phuongmt08/uwb-rtls/docs/assets/diagrams/thesis/chapter4/figure-4-2-firmware-startup-flow.png

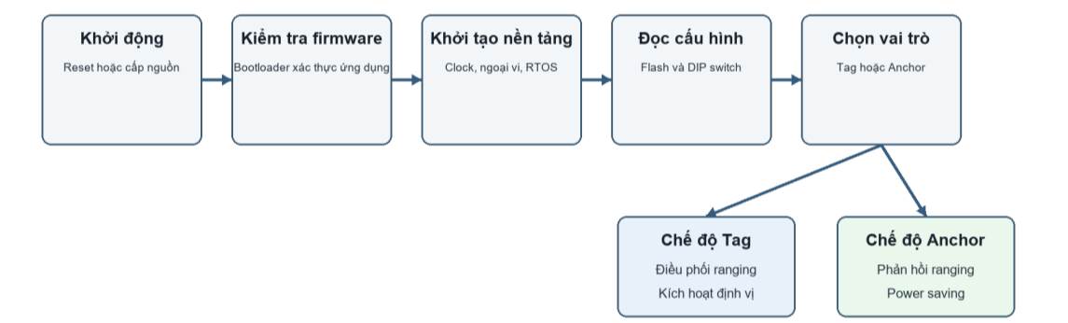
docs/assets/diagrams/thesis/chapter4/figure-4-2-firmware-startup-flow.png
