phuongmt08/uwb-rtls/docs/assets/diagrams/thesis/chapter4/figure-4-7-flash-write-and-swap-flow.png

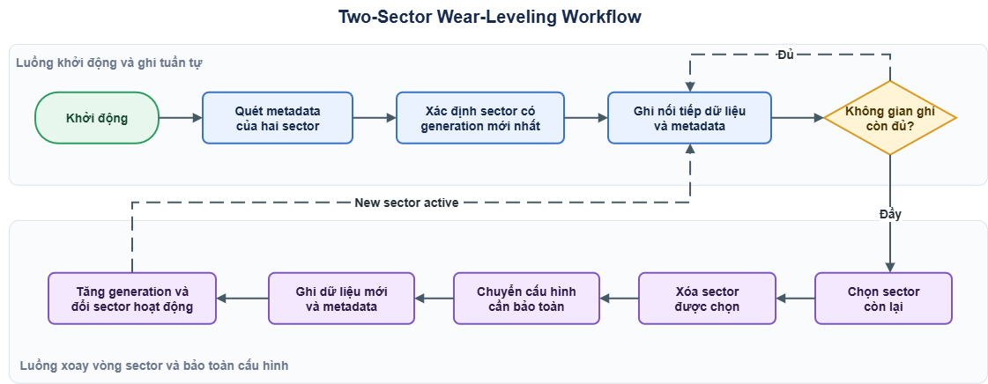
docs/assets/diagrams/thesis/chapter4/figure-4-7-flash-write-and-swap-flow.png
