phuongmt08/uwb-rtls/docs/assets/diagrams/thesis/chapter4/figure-4-18-ble-connection-flow.png

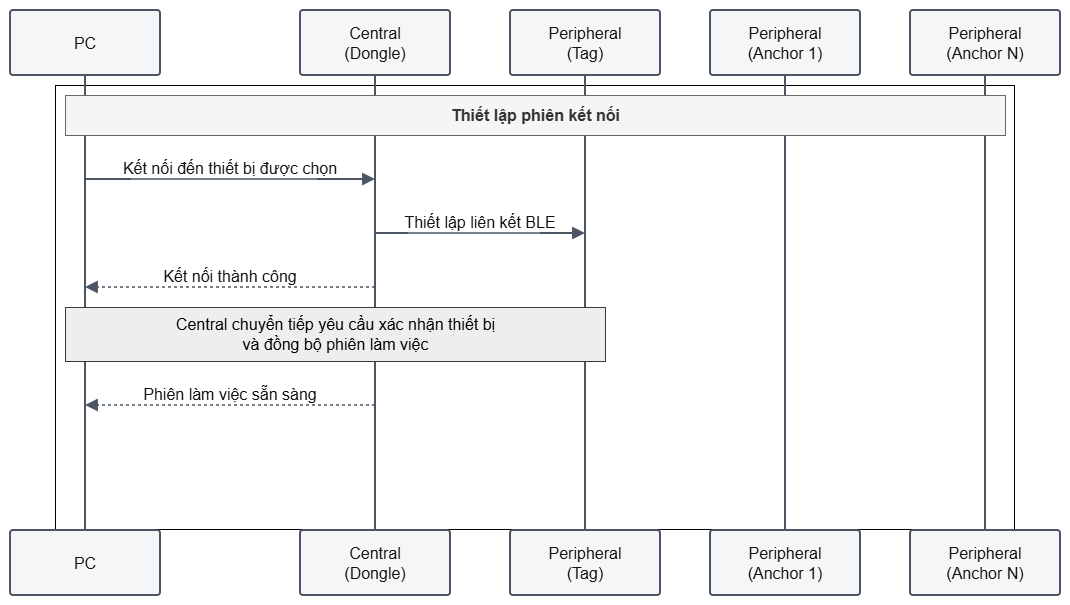
docs/assets/diagrams/thesis/chapter4/figure-4-18-ble-connection-flow.png
