phuongmt08/uwb-rtls/docs/assets/diagrams/thesis/chapter4/figure-4-19-ble-data-exchange-flow.png

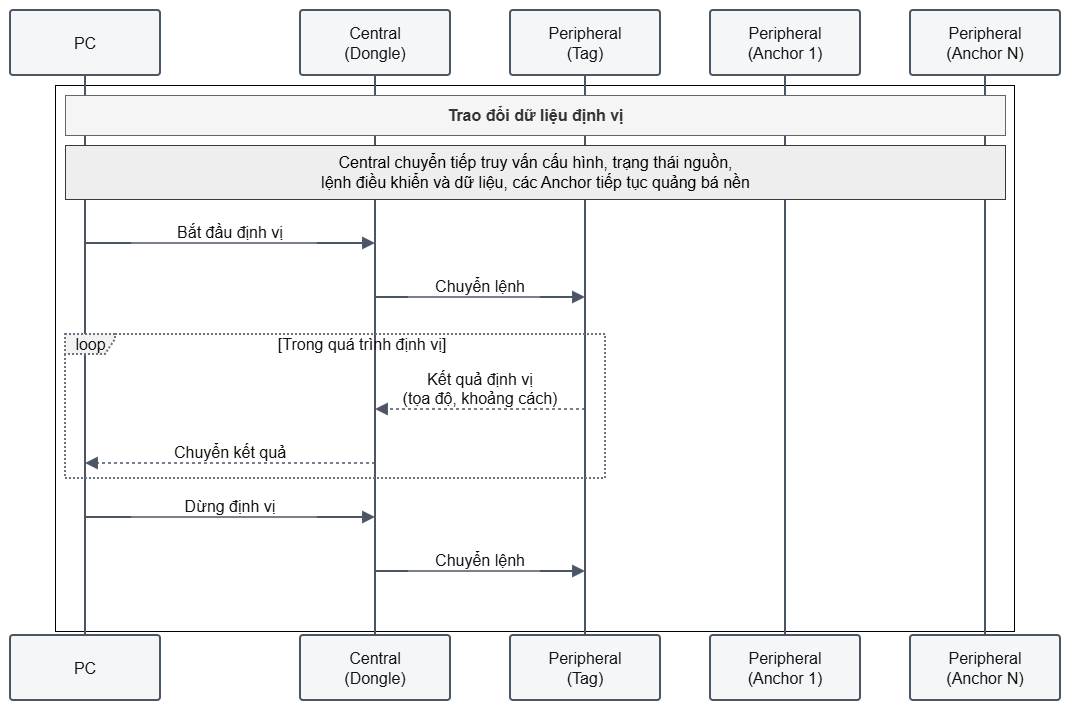
docs/assets/diagrams/thesis/chapter4/figure-4-19-ble-data-exchange-flow.png
