phuongmt08/uwb-rtls/docs/assets/images/thesis/chapter4/figure-4-15-nlos-cir-sample-mask.png

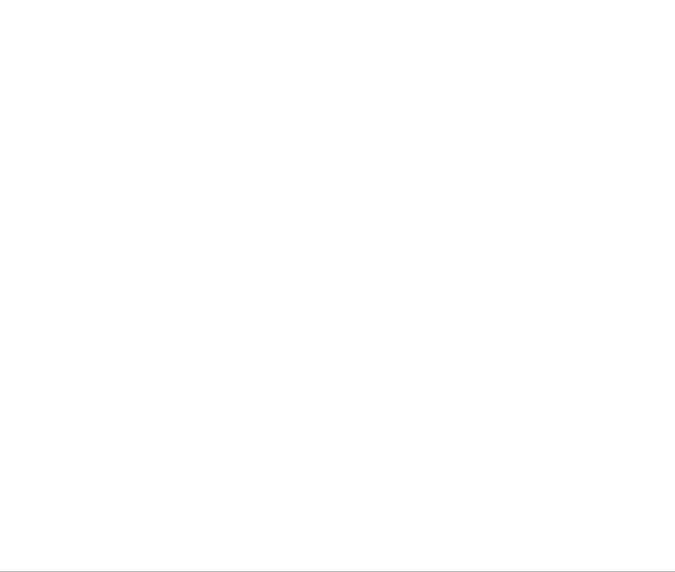
docs/assets/images/thesis/chapter4/figure-4-15-nlos-cir-sample-mask.png
