phuongmt08/uwb-rtls/docs/assets/images/thesis/raw/thesis-image-001.png

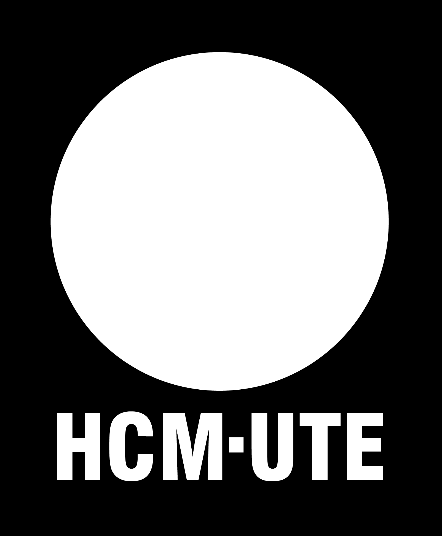
docs/assets/images/thesis/raw/thesis-image-001.png
