phuongmt08/uwb-rtls/docs/assets/images/thesis/raw/thesis-image-028.png

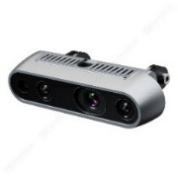
docs/assets/images/thesis/raw/thesis-image-028.png
