phuongmt08/uwb-rtls/docs/assets/images/thesis/raw/thesis-image-029.png

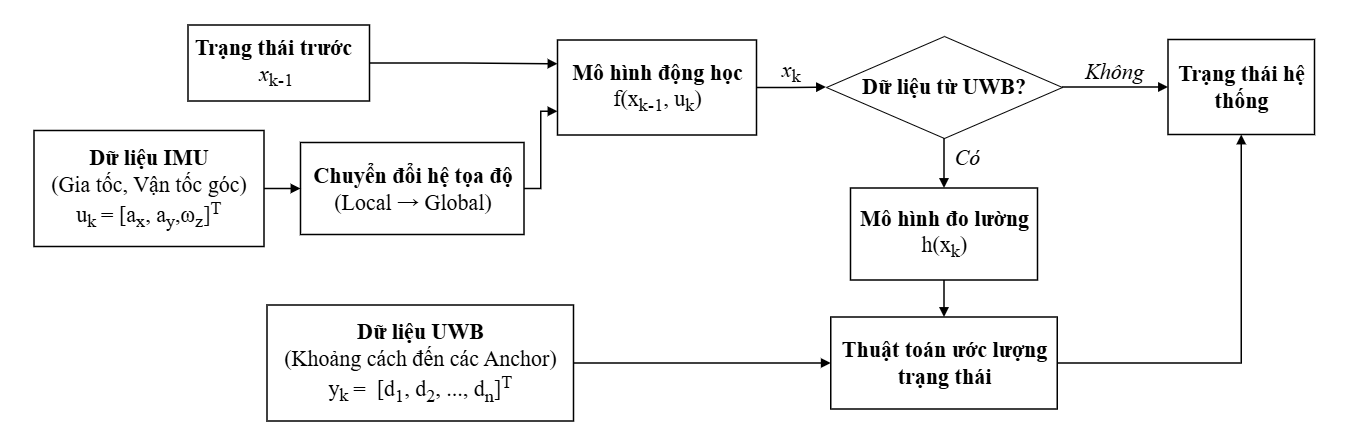
docs/assets/images/thesis/raw/thesis-image-029.png
