phuongmt08/uwb-rtls/docs/assets/images/thesis/raw/thesis-image-034.png

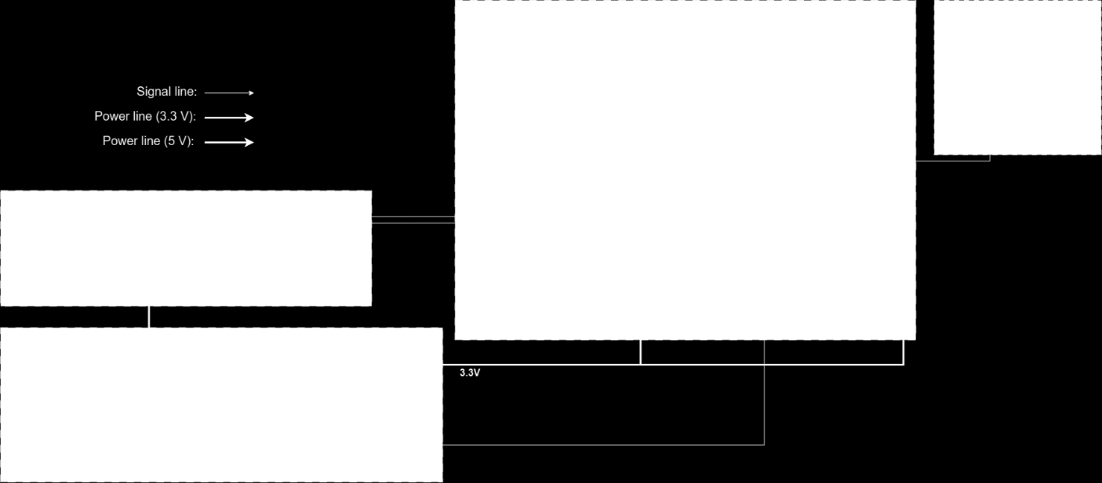
docs/assets/images/thesis/raw/thesis-image-034.png
