phuongmt08/uwb-rtls/docs/assets/images/thesis/raw/thesis-image-037.png

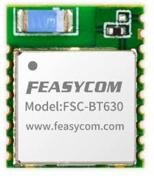
docs/assets/images/thesis/raw/thesis-image-037.png
