phuongmt08/uwb-rtls/docs/assets/images/thesis/raw/thesis-image-058.png

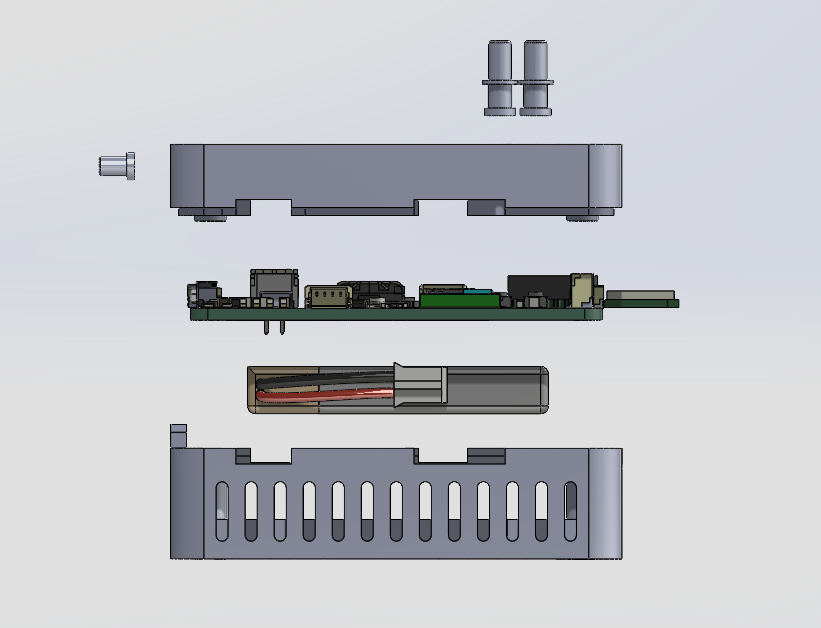
docs/assets/images/thesis/raw/thesis-image-058.png
