phuongmt08/uwb-rtls/docs/assets/images/thesis/raw/thesis-image-059.png

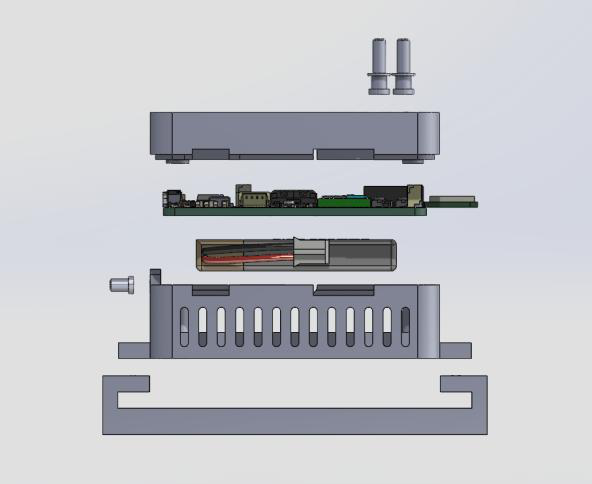
docs/assets/images/thesis/raw/thesis-image-059.png
