phuongmt08/uwb-rtls/docs/assets/images/thesis/raw/thesis-image-092.png

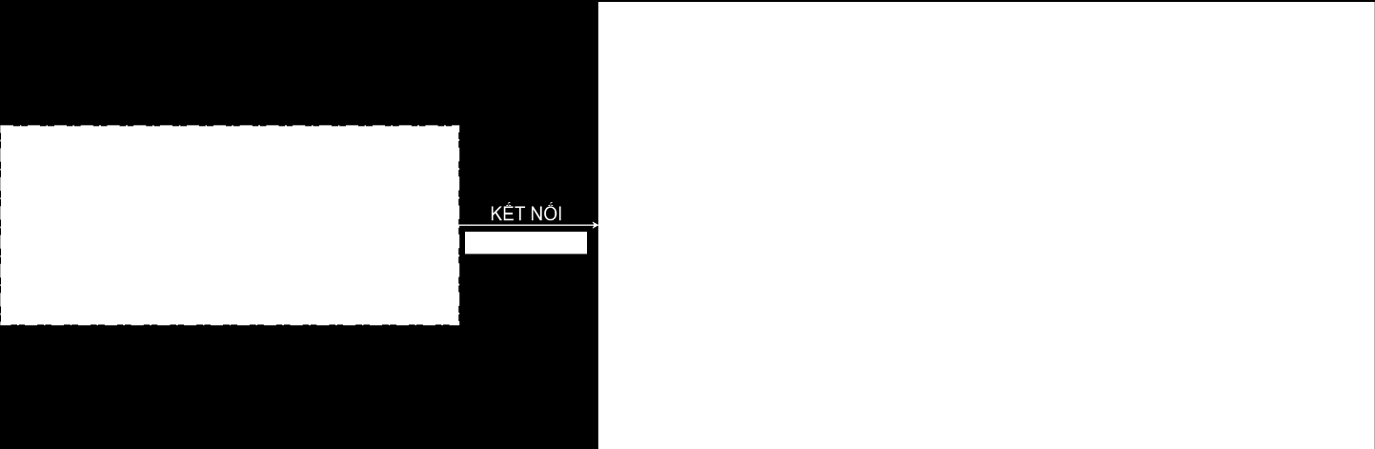
docs/assets/images/thesis/raw/thesis-image-092.png
