phuongmt08/uwb-rtls/docs/assets/images/thesis/raw/thesis-image-096.png

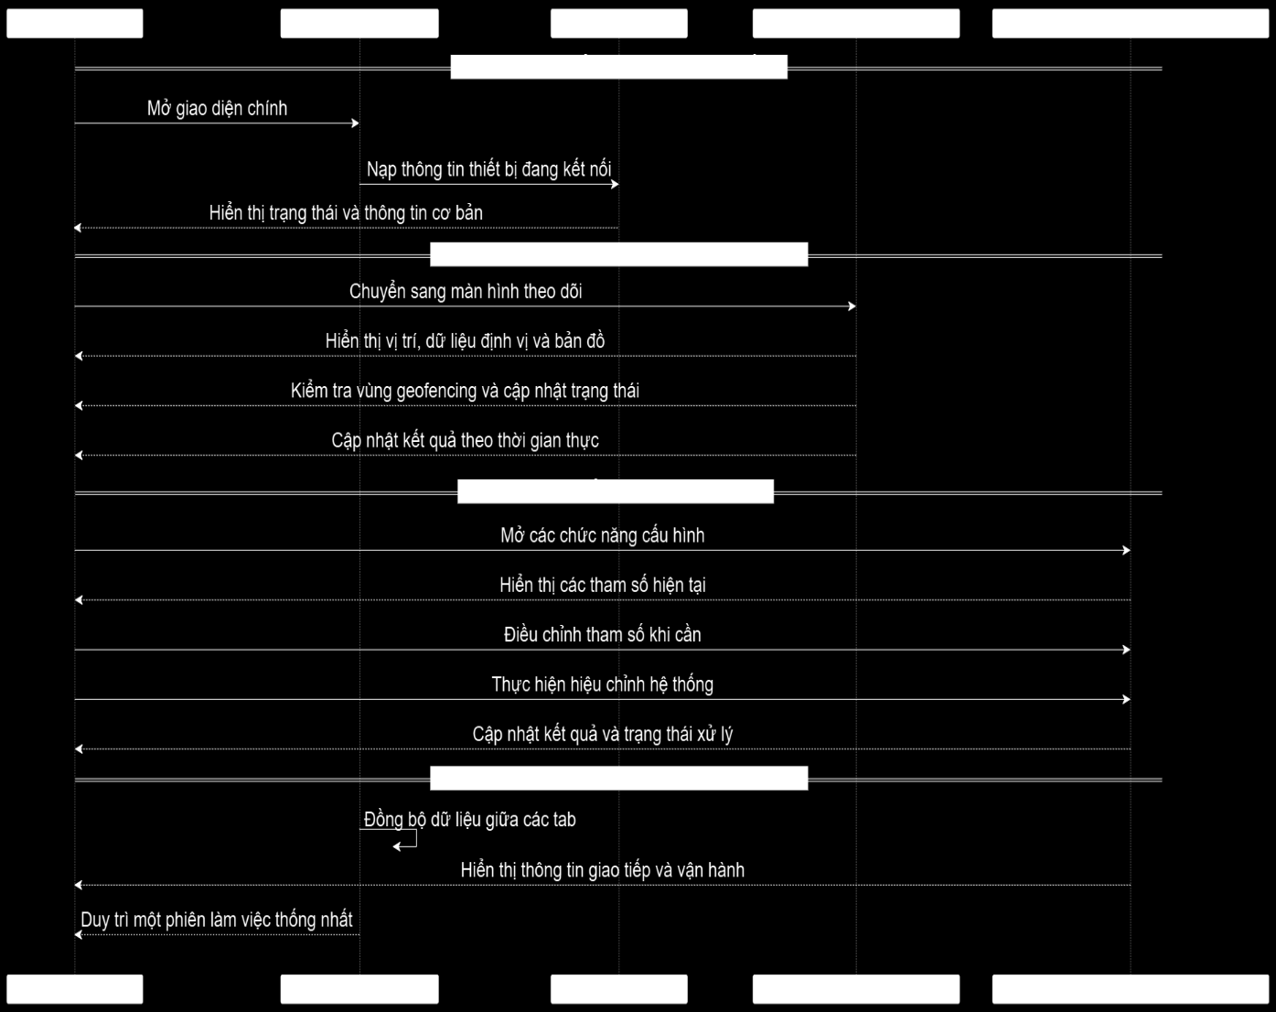
docs/assets/images/thesis/raw/thesis-image-096.png
