phuongmt08/uwb-rtls/docs/assets/images/thesis/raw/thesis-image-098.png

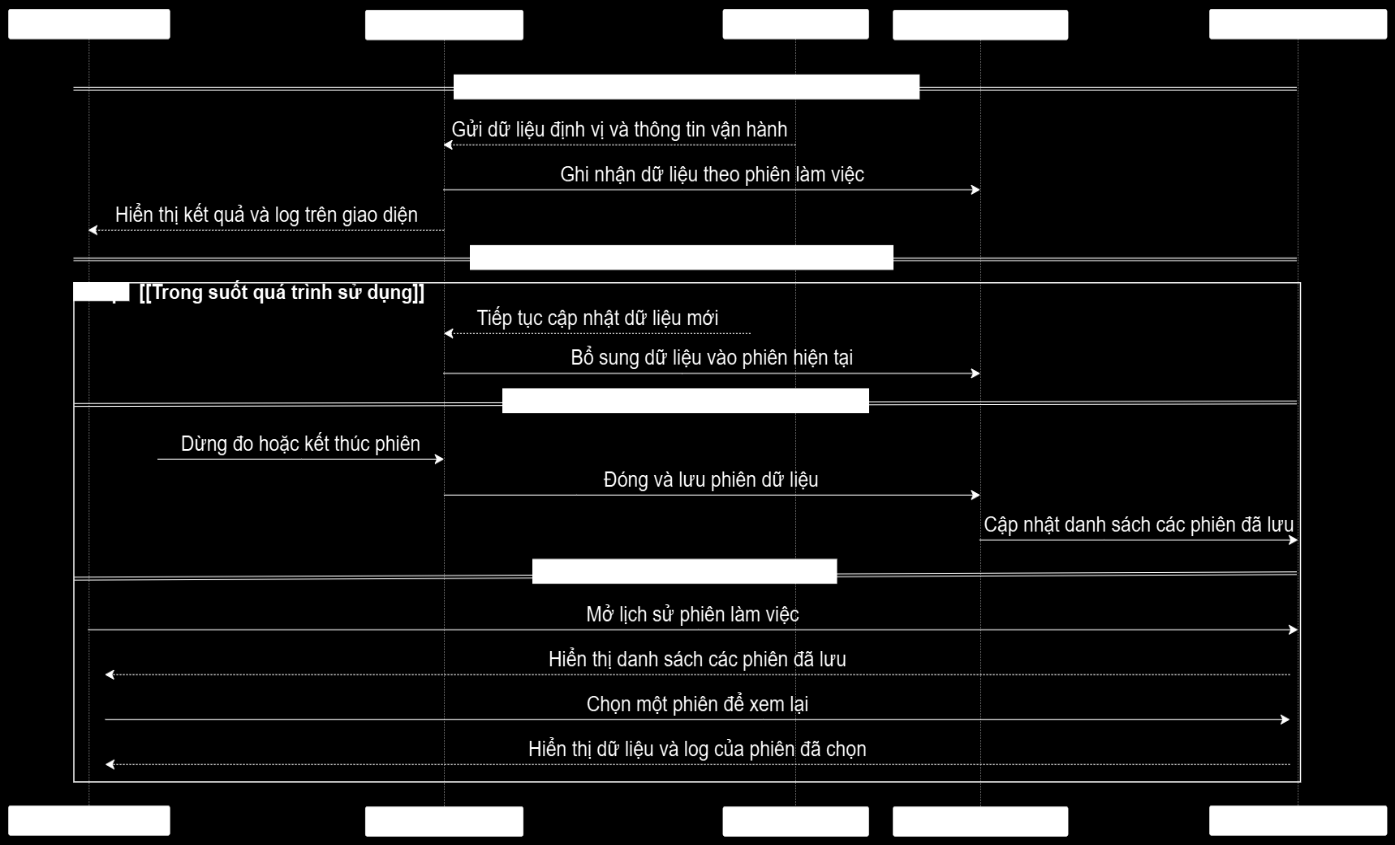
docs/assets/images/thesis/raw/thesis-image-098.png
