phuongmt08/uwb-rtls/docs/assets/images/thesis/raw/thesis-image-110.png

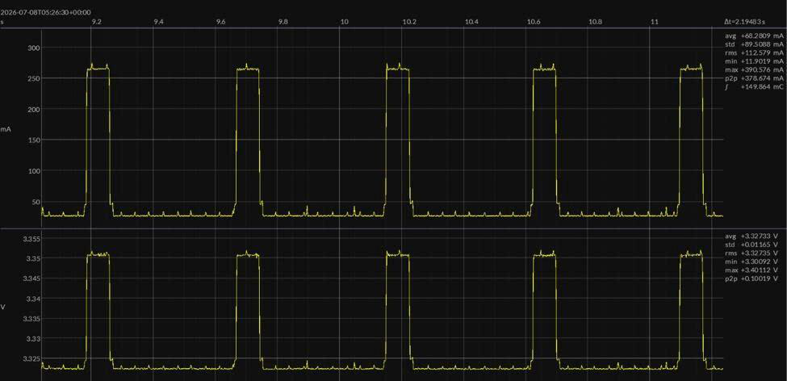
docs/assets/images/thesis/raw/thesis-image-110.png
