phuongmt08/uwb-rtls/docs/assets/images/thesis/raw/thesis-image-129.png

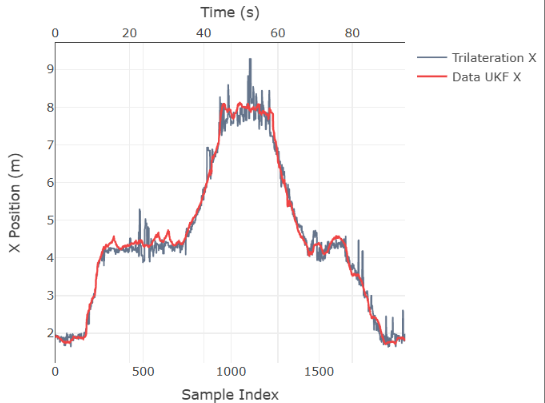
docs/assets/images/thesis/raw/thesis-image-129.png
