phuongmt08/uwb-rtls/docs/assets/images/thesis/raw/thesis-image-131.png

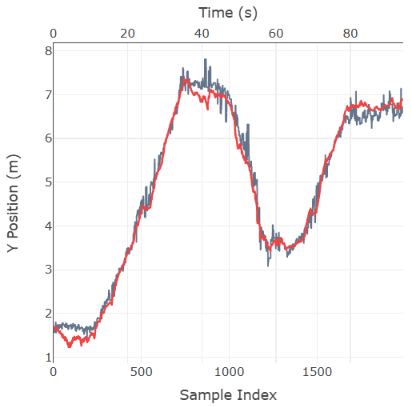
docs/assets/images/thesis/raw/thesis-image-131.png
