phuongmt08/uwb-rtls/docs/assets/images/thesis/raw/thesis-image-139.png

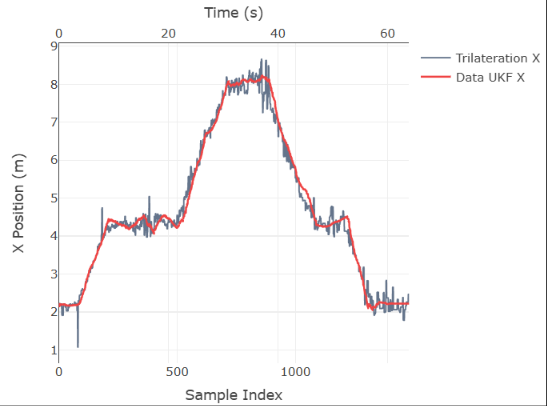
docs/assets/images/thesis/raw/thesis-image-139.png
