phuongmt08/uwb-rtls/docs/assets/images/thesis/raw/thesis-image-141.png

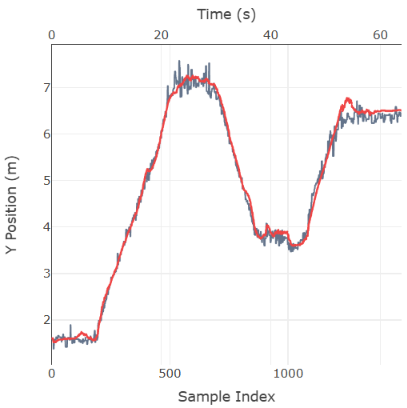
docs/assets/images/thesis/raw/thesis-image-141.png
