phuongmt08/uwb-rtls/hardware/anchor/rev0.1/rev0.1_backward.png

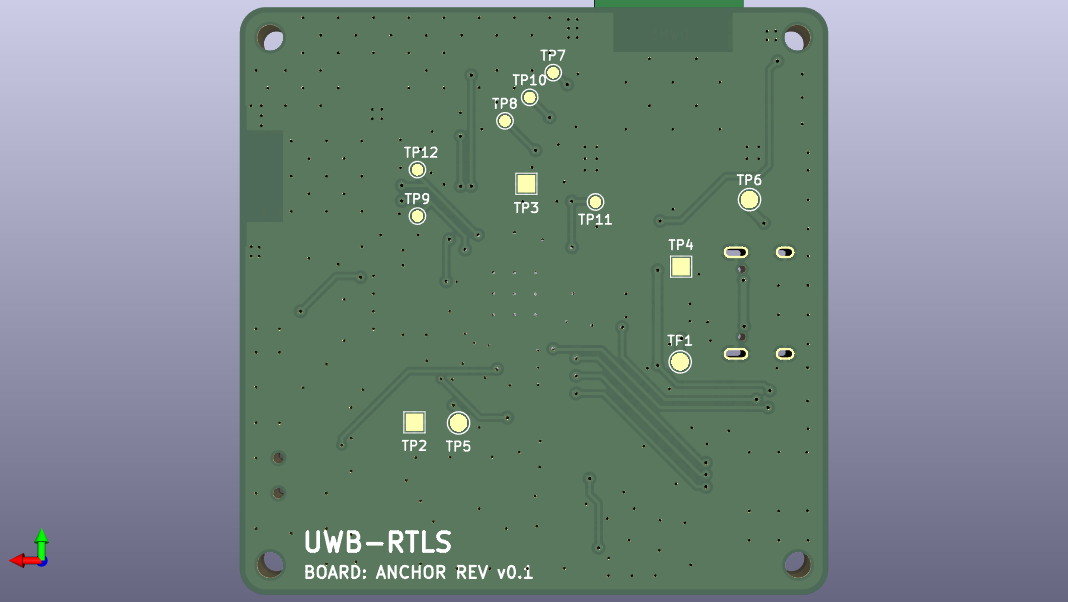
hardware/anchor/rev0.1/rev0.1_backward.png
