phuongmt08/uwb-rtls/hardware/anchor/rev0.1/rev0.1_forward.png

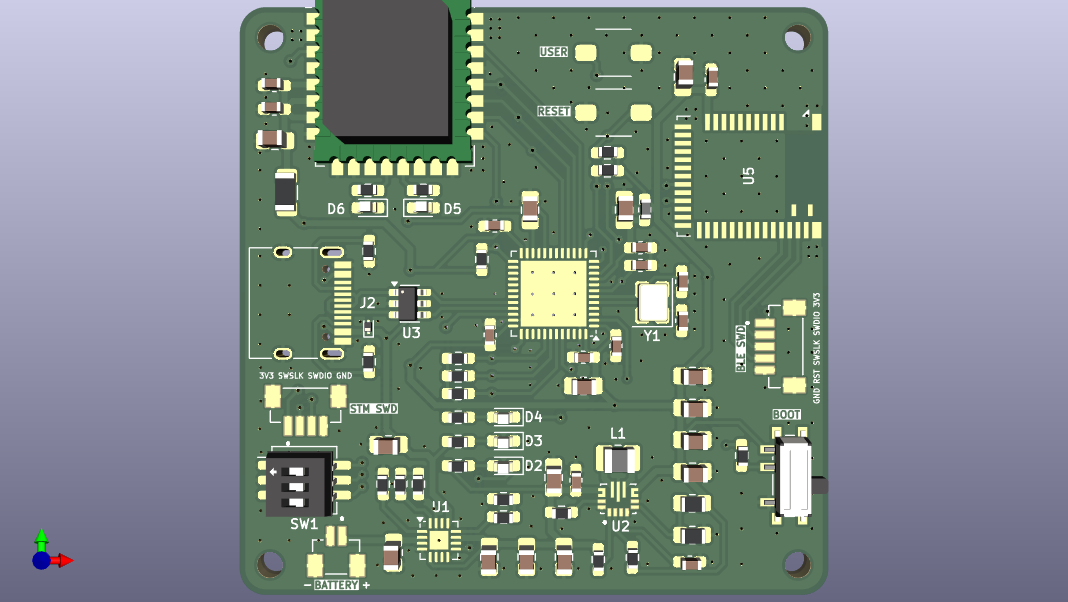
hardware/anchor/rev0.1/rev0.1_forward.png
