phuongmt08/uwb-rtls/tmp/pdfs/you2020/page-03.png

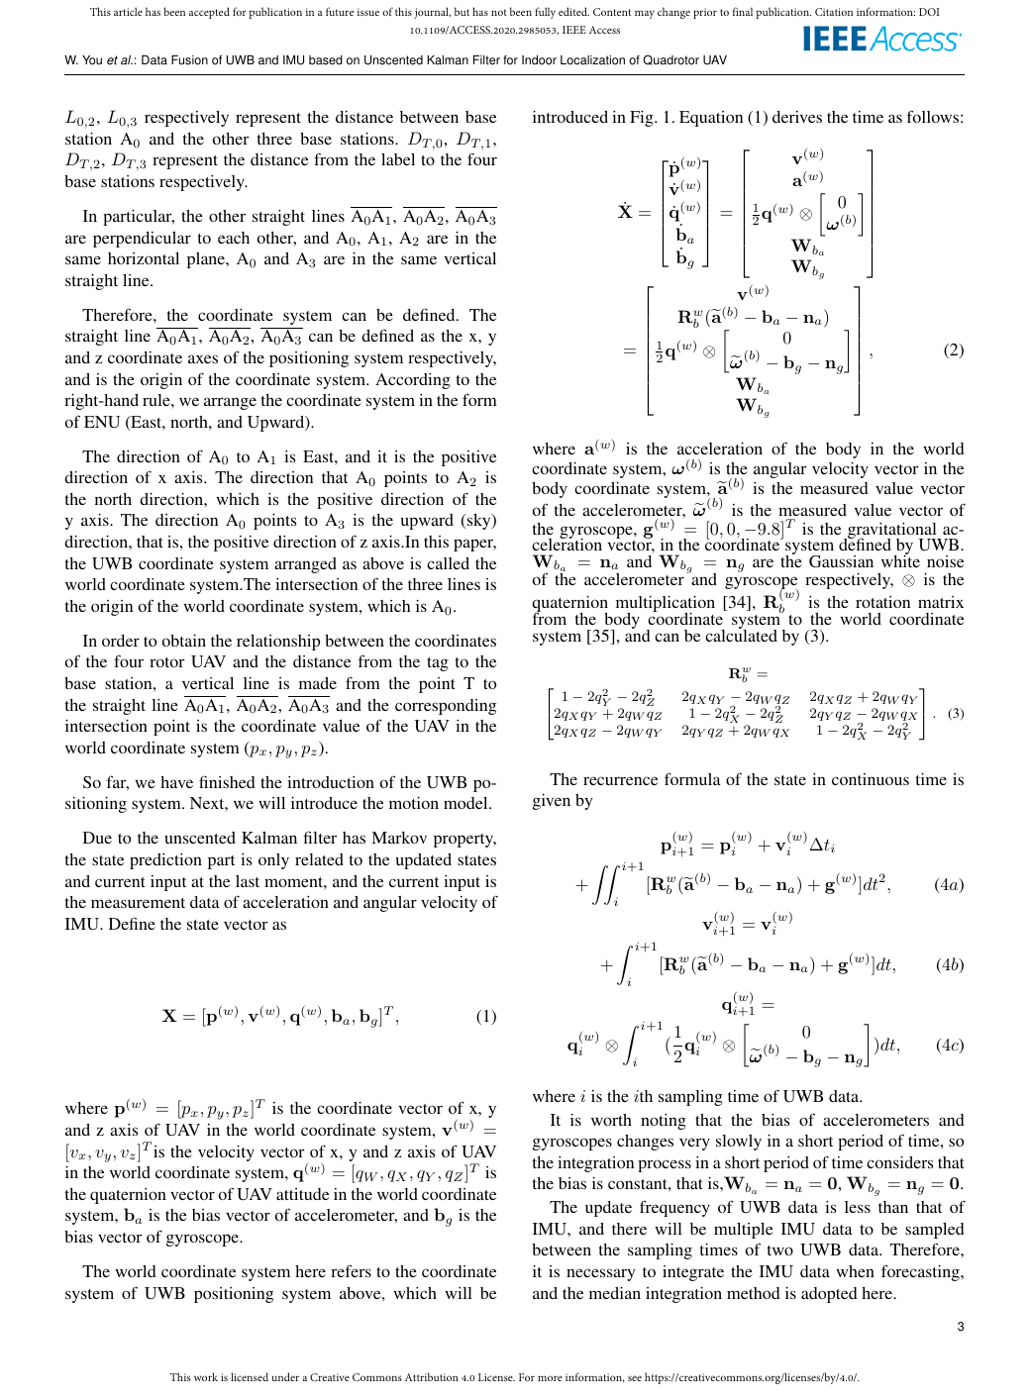
tmp/pdfs/you2020/page-03.png
