phuongmt08/uwb-rtls/tmp/pdfs/you2020/page-05.png

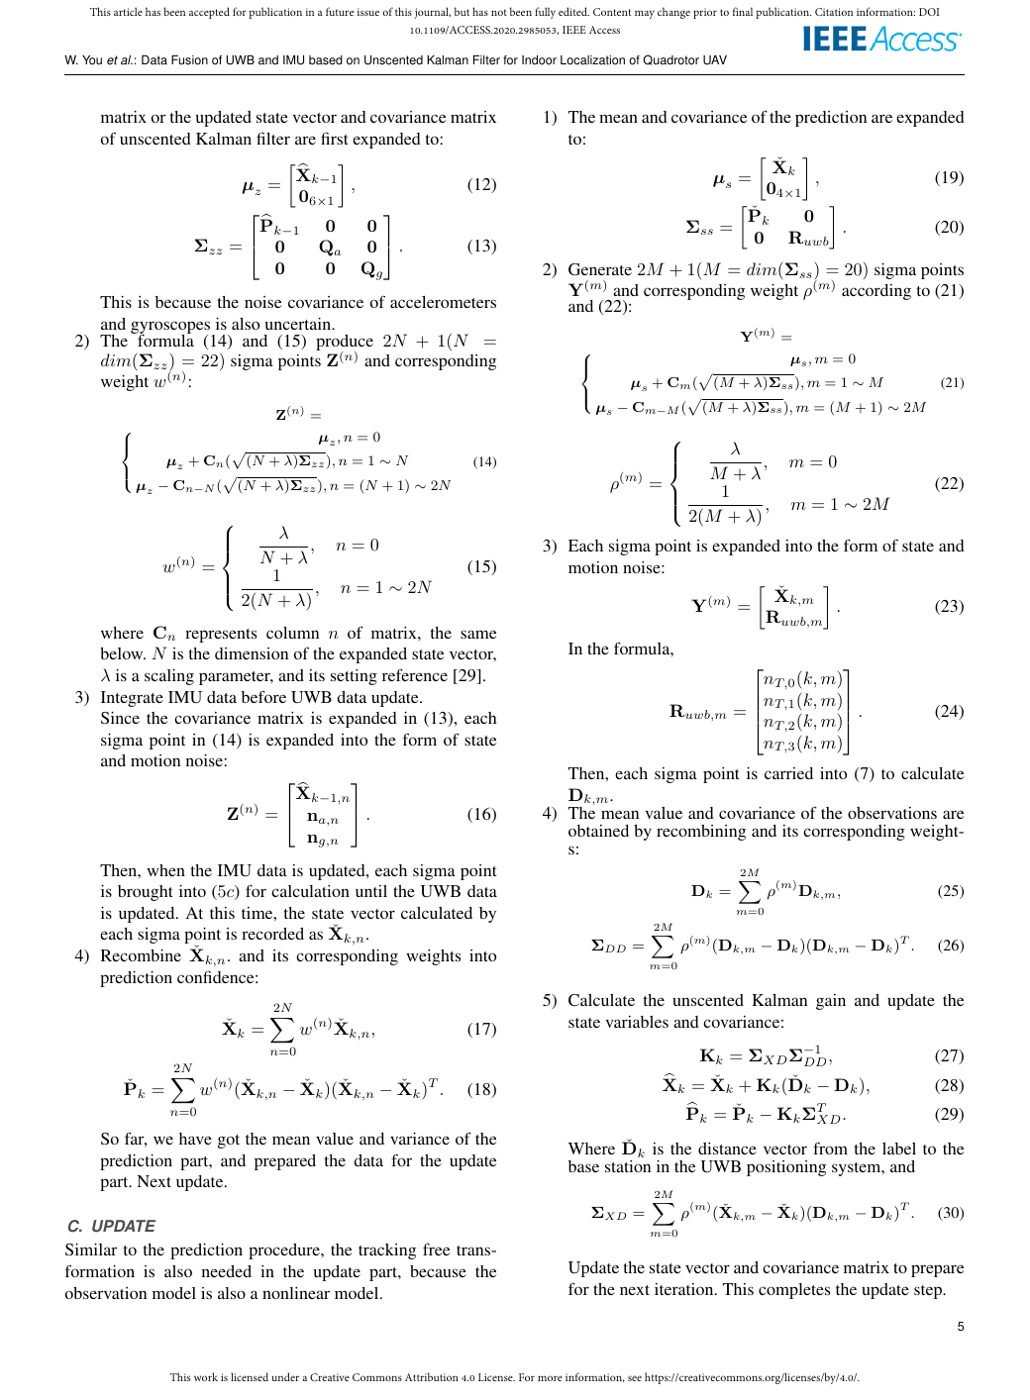
tmp/pdfs/you2020/page-05.png
