phuongmt08/uwb-rtls/firmware/uwb/sys/sys_sensor_fusion.c

/**
 * @file       sys_sensor_fusion.c
 * @copyright  [Your Copyright]
 * @license    [Your License]
 * @version    1.0.0
 * @date       25/03/26
 * @author     Dong Son
 *
 * @brief
 */
/* Includes ----------------------------------------------------------- */
#include "config.h"
#include "sys_sensor_fusion.h"
#include "bsp_imu.h"
#include "positioning_config.h"
#include "bsp_io.h"
#include "bsp_util.h"
#include "err.h"
#include "mw_filter.h"
#include "network/network_cmd.h"
#include <stddef.h>
#include <math.h>
#include <string.h>
#include <stdio.h>
#include "sys_config.h"
#include "ble/sys_ble_peripheral.h"
#include "sys_logger.h"
#include "cmsis_os2.h"
#include "app_rtos_handles.h"

/* Private defines ---------------------------------------------------- */
#define NUM_STATE     			8
#define NUM_PREDICT_NOISE     	3
#define NUM_UPDATE_NOISE     	3
#define N       				(NUM_STATE + NUM_PREDICT_NOISE)
#define M						(NUM_STATE + NUM_UPDATE_NOISE)
#define NUM_PREDICT_SIGMA  		(2*N + 1)
#define NUM_UPDATE_SIGMA  		(2*M + 1)

#define UKF_ALPHA               SYS_FUSION_UKF_ALPHA
#define UKF_KAPPA               SYS_FUSION_UKF_KAPPA
#define UKF_BETA                SYS_FUSION_UKF_BETA
#define N_PLUS_LAMBDA_N         (UKF_ALPHA * UKF_ALPHA * (N + UKF_KAPPA))
#define UKF_LAMBDA_N  			(N_PLUS_LAMBDA_N - N)
#define GAMMA_N       			sqrtf(N_PLUS_LAMBDA_N)
#define M_PLUS_LAMBDA_M         (UKF_ALPHA * UKF_ALPHA * (M + UKF_KAPPA))
#define UKF_LAMBDA_M  			(M_PLUS_LAMBDA_M - M)
#define GAMMA_M       			sqrtf(M_PLUS_LAMBDA_M)

#define Qa						SYS_FUSION_UKF_QA
#define Qg						SYS_FUSION_UKF_QG
#define R_uwb					SYS_FUSION_UKF_R_UWB

#define SYS_SENSOR_FUSION_PI    3.14159265358979323846f
#define SYS_SENSOR_FUSION_2PI   (2.0f * SYS_SENSOR_FUSION_PI)
#define RAD2DEG							180.0f / 3.14159265358979323846f
#define DEG2RAD							3.14159265358979323846f / 180.0f

#define TEST_UKF_STREAM_MASK_PACKET_COUNT  50U
#define TEST_UKF_STREAM_ANCHOR_COUNT       4U
#define SYS_FUSION_PREDICT_TIMEOUT_MS      2000U
/* Temporary A/B diagnostic: keep draining the IMU queue, but do not propagate
 * the UKF state/covariance. Set to 0 after comparing update-only vs normal. */
#define SYS_FUSION_DIAGNOSTIC_DISABLE_PREDICT  0
/* Temporary pipeline diagnostic: publish the current trilateration position as
 * the fusion position, bypassing the UKF range-measurement update entirely. */
#define SYS_FUSION_DIAGNOSTIC_USE_TRIL_POSITION  0
/* Reuse sensor_fusion_result as an update diagnostic packet. The host-side
 * ukf_update_diagnostic.py parser owns the field mapping for ukf_step 101. */
#define SYS_FUSION_DIAGNOSTIC_UPDATE_PACKET      0
#define SYS_FUSION_DIAGNOSTIC_UPDATE_STEP        101U
#define SYS_FUSION_DIAGNOSTIC_WEIGHT_SCALE       1000000.0f

/* Private enumerate/structure ---------------------------------------- */
typedef struct
{
	sys_sensor_fusion_data_t state;

    float32_t P_data[NUM_STATE * NUM_STATE]; 					// P [8x8]
    float32_t Q_data[NUM_PREDICT_NOISE * NUM_PREDICT_NOISE]; 	// Q [3x3]
    float32_t R_data[NUM_UPDATE_NOISE * NUM_UPDATE_NOISE]; 		// R [3x3]

    // Weights
    float32_t Wm_N[NUM_PREDICT_SIGMA];
	float32_t Wc_N[NUM_PREDICT_SIGMA];
	float32_t Wm_M[NUM_UPDATE_SIGMA];
	float32_t Wc_M[NUM_UPDATE_SIGMA];

	bool is_first_frame;
	float32_t X_sigma_pred[NUM_STATE][NUM_PREDICT_SIGMA];
	float32_t Noise_sigma_pred[NUM_PREDICT_NOISE][NUM_PREDICT_SIGMA];

    bsp_imu_data_t imu_old;
    bsp_imu_data_t imu_current;

    // Instances của CMSIS-DSP
    arm_matrix_instance_f32 mat_P;
    arm_matrix_instance_f32 mat_Q;
    arm_matrix_instance_f32 mat_R;

	// Flag
	bool enable_predict;
	bool enable_update;
	bool initialized;
	bool has_predict_tick;
	uint32_t last_predict_tick;
	uint32_t last_update_tick;

} ukf_core_t;

typedef struct
{
    bool valid;
    float tril_x;
    float tril_y;
    float prior_px;
    float prior_py;
    float posterior_px;
    float posterior_py;
    float d_real[NUM_UPDATE_NOISE];
    float d_mean[NUM_UPDATE_NOISE];
    float r_diag[NUM_UPDATE_NOISE];
    float prior_pxx;
    float prior_pxy;
    float prior_pyy;
    uint8_t anchor_ids[NUM_UPDATE_NOISE];
} ukf_update_diagnostic_t;

// Filter
typedef struct
{
    float32_t x1;
    float32_t x2;
    float32_t y1;
    float32_t y2;
} imu_biquad_filter_t;

typedef struct
{
    imu_biquad_filter_t ax;
    imu_biquad_filter_t ay;
    imu_biquad_filter_t az;
    imu_biquad_filter_t gx;
    imu_biquad_filter_t gy;
    imu_biquad_filter_t gz;
    bool butterworth_initialized;
    bool attitude_initialized;
    float roll;
    float pitch;
    uint16_t zupt_count;
    bool zupt_active;
} imu_conditioner_t;

/* Private macros ----------------------------------------------------- */
/* Public variables --------------------------------------------------- */
extern network_core_t g_network_core;
extern bool g_ranging_enabled;

/* Private variables -------------------------------------------------- */
// filter
static ukf_init_filter_t s_ukf_init_filter;
static ukf_init_distance_filter_t s_ukf_init_dist_filter;
static imu_conditioner_t s_imu_conditioner = {0};
static bsp_imu_bias_t s_imu_bias = {0};
// log
float yaw = 0.0f;
float b_gz_t = 0.0f;
static float 	s_latest_distances[NUM_ANCHORS] = {0.0f};
static double 	s_latest_fp_amp_norm[NUM_ANCHORS] = {0.0};
static double 	s_latest_fp_snr[NUM_ANCHORS] = {0.0};
static protobuf_anchor_data_t s_latest_anchor_data[pb_arraysize(protobuf_sensor_fusion_result_t, anchors)] = {0};
static pb_size_t s_latest_anchor_data_count = 0U;
static uint32_t s_error_count = 0U;
static uint32_t s_latest_ranging_error_count = 0U;
static uint32_t s_prefilter_reject_count = 0U;
static uint8_t 	s_last_selected_anchors_mask = 0U;
static float 	s_latest_tril_x = 0.0f;
static float 	s_latest_tril_y = 0.0f;
static float 	s_fusion_dt = 0.0f;
// debug
static uint16_t predict_delta_ms = 0;
static uint16_t update_delta_ms = 0;
unsigned long sys_predict_count = 0;
unsigned long sys_update_count = 0;
unsigned long sys_predict_err_count = 0;
unsigned long sys_update_err_count = 0;
unsigned long sys_update_cholesky_err_count = 0;
unsigned long sys_update_inverse_err_count = 0;
//
static ukf_core_t ukf 	= {0};
static ukf_update_diagnostic_t s_update_diagnostic = {0};
float yaw_rad_cached   	= 0.0f;

#if TEST_UKF_STREAM_BLE || TEST_UKF_STREAM_UART
static uint32_t s_stream_test_sample_idx = 0U;
#endif
#if TEST_UKF_STREAM_BLE && TEST_UKF_STREAM_FUSION_LOG && ENABLE_SYS_FUSION
static uint32_t s_stream_test_tx_frame_cnt = 0U;
#endif

/* Private function prototypes ---------------------------------------- */
static float normalize_angle(float angle);
static float calc_dt(void);
static void reset_runtime_state(void);
static bool active_anchor_index_for_id(uint8_t anchor_id, uint8_t *index_out);
static void clear_latest_anchor_metrics(void);
static const mw_tril_anchor_t *find_anchor_by_id(const mw_tril_anchor_t *anchors,
                                                uint8_t anchor_count,
                                                uint8_t anchor_id);
static void snapshot_latest_anchor_metrics(const mw_tril_anchor_t *candidate_anchors,
                                           uint8_t candidate_count);
static void update_latest_anchor_data_snapshot(const uwb_distance_msg_t *ranging_msg,
                                               const mw_tril_anchor_t selected_anchors[3]);
static int16_t to_uart_fixed2(float value);
static int32_t to_proto_fixed2(float value);
static int32_t to_proto_fixed3(float value);
static int32_t to_scaled_i32(float value, float scale);
static uint32_t to_mm_u32(float value);
#if TEST_UKF_STREAM_BLE && ENABLE_SYS_FUSION
static void configure_adv(network_core_t *stream);
#endif
sys_sensor_fusion_err_t fusion_update(sys_sensor_fusion_data_t *p_ukf,
                                                 float d0,
                                                 float d1,
                                                 float d2,
                                                 const uint8_t anchor_ids[3]);

// Filter
static void reset_imu_conditioner(void);
static bsp_imu_data_t condition_imu_sample(const bsp_imu_data_t *raw, float dt);
static void reset_biquad_filter(imu_biquad_filter_t *filter, float value);
static float apply_butterworth_2nd_order(imu_biquad_filter_t *filter, float x, float dt);
static void compensate_gravity(bsp_imu_data_t *sample, float dt);
static void update_zupt_state(const bsp_imu_data_t *raw, const bsp_imu_data_t *conditioned);
static void apply_zupt_velocity_constraint(void);
static bool invert_innovation_covariance(const float32_t covariance[9],
                                         float32_t inverse[9]);
static void stabilize_state_covariance(void);

/* Function definitions ----------------------------------------------- */
sys_sensor_fusion_err_t sys_sensor_fusion_init(sys_sensor_fusion_data_t *p_ukf)
{
	CHECK_ERR(p_ukf != NULL, SYS_SENSOR_FUSION_ERR);

	/* IMU hardware initialization and calibration are owned by main().
	 * Fusion reset may run repeatedly at runtime, so it must not soft-reset or
	 * recalibrate the shared IMU device. */
	if (!bsp_imu_is_initialized())
	{
		RLOG_W(LOG_OBJECT_CODE_TAG,
		       "[FUSION] IMU is not initialized; UKF initialization skipped");
		return SYS_SENSOR_FUSION_ERR;
	}

	bsp_imu_bias_t imu_bias;

	if (bsp_imu_get_bias_data(&imu_bias) != BSP_IMU_OK)
	{
		RLOG_W(LOG_OBJECT_CODE_TAG,
		       "[FUSION] Failed to read IMU bias; UKF initialization skipped");
		return SYS_SENSOR_FUSION_ERR;
	}

	memset(&ukf, 0, sizeof(ukf));
	yaw = 0.0f;
	/* Convert the calibration values to the fusion body frame. The single-pose
	 * accelerometer means contain gravity, so they must not be used as planar
	 * linear-acceleration biases after gravity compensation. */
	s_imu_bias.bias_ax = -imu_bias.bias_ay;
	s_imu_bias.bias_ay = imu_bias.bias_ax;
	s_imu_bias.bias_az = imu_bias.bias_az;
	s_imu_bias.bias_gx = -imu_bias.bias_gy;
	s_imu_bias.bias_gy = imu_bias.bias_gx;
	s_imu_bias.bias_gz = imu_bias.bias_gz;
#if SYS_FUSION_IMU_PREFILTER_ENABLE
	ukf.state.b_ax = 0.0f;
	ukf.state.b_ay = 0.0f;
#else
	ukf.state.b_ax = -imu_bias.bias_ay;
	ukf.state.b_ay = imu_bias.bias_ax;
#endif
	ukf.state.b_gz = imu_bias.bias_gz;
	b_gz_t = imu_bias.bias_gz;

	// P
    for(int i=0; i<64; i++) ukf.P_data[i] = 0.0f;
	ukf.P_data[0] 	= SYS_FUSION_UKF_INIT_P_PX;  	// p_x
	ukf.P_data[9] 	= SYS_FUSION_UKF_INIT_P_PY;   	// p_y
	ukf.P_data[18] 	= SYS_FUSION_UKF_INIT_P_VX; 	// v_x
	ukf.P_data[27] 	= SYS_FUSION_UKF_INIT_P_VY;  	// v_y
	ukf.P_data[36] 	= SYS_FUSION_UKF_INIT_P_THETA;  	// theta
	ukf.P_data[45] 	= SYS_FUSION_UKF_INIT_P_BIAS_AX; 	// Bias
	ukf.P_data[54] 	= SYS_FUSION_UKF_INIT_P_BIAS_AY;
	ukf.P_data[63] 	= SYS_FUSION_UKF_INIT_P_BIAS_GZ;

    // Q
    for(int i=0; i<9; i++) ukf.Q_data[i] = 0.0f;
    ukf.Q_data[0] = Qa;
    ukf.Q_data[4] = Qa;
    ukf.Q_data[8] = Qg;

    // R
    for(int i=0; i<9; i++) ukf.R_data[i] = 0.0f;
    ukf.R_data[0] = R_uwb;
    ukf.R_data[4] = R_uwb;
    ukf.R_data[8] = R_uwb;

    // Sigma
    ukf.Wm_N[0] = UKF_LAMBDA_N / (N + UKF_LAMBDA_N);
	ukf.Wc_N[0] = ukf.Wm_N[0] + (1.0f - UKF_ALPHA * UKF_ALPHA + UKF_BETA);
	float w_rest_n = 1.0f / (2.0f * (N + UKF_LAMBDA_N));
	for(int i=1; i<NUM_PREDICT_SIGMA; i++)
	{
		ukf.Wm_N[i] = w_rest_n;
		ukf.Wc_N[i] = w_rest_n;
	}

	ukf.Wm_M[0] = UKF_LAMBDA_M / (M + UKF_LAMBDA_M);
	ukf.Wc_M[0] = ukf.Wm_M[0] + (1.0f - UKF_ALPHA * UKF_ALPHA + UKF_BETA);
	float w_rest_m = 1.0f / (2.0f * (M + UKF_LAMBDA_M));
	for(int i=1; i<NUM_UPDATE_SIGMA; i++)
	{
		ukf.Wm_M[i] = w_rest_m;
		ukf.Wc_M[i] = w_rest_m;
	}

	// Matrix
    arm_mat_init_f32(&ukf.mat_P, NUM_STATE, NUM_STATE, ukf.P_data);
    arm_mat_init_f32(&ukf.mat_Q, NUM_PREDICT_NOISE, NUM_PREDICT_NOISE, ukf.Q_data);
    arm_mat_init_f32(&ukf.mat_R, NUM_UPDATE_NOISE, NUM_UPDATE_NOISE, ukf.R_data);

    *p_ukf = ukf.state;

    ukf.is_first_frame = true;
    ukf.initialized = false;
    ukf.has_predict_tick = false;
    ukf.last_predict_tick = 0U;
    ukf.last_update_tick = 0U;
    sys_sensor_fusion_clear_update_flag();
    sys_sensor_fusion_clear_predict_flag();
    reset_runtime_state();

#if SYS_FUSION_IMU_PREFILTER_ENABLE
    /* Calibration was captured while stationary, so it is a better initial
     * gravity direction than the first predict sample (which may arrive after
     * the chair has already started moving). */
    const float calib_acc_norm = sqrtf(s_imu_bias.bias_ax * s_imu_bias.bias_ax
                                     + s_imu_bias.bias_ay * s_imu_bias.bias_ay
                                     + s_imu_bias.bias_az * s_imu_bias.bias_az);
    if (calib_acc_norm > 0.1f)
    {
        s_imu_conditioner.roll = atan2f(s_imu_bias.bias_ay,
                                        s_imu_bias.bias_az);
        s_imu_conditioner.pitch = atan2f(-s_imu_bias.bias_ax,
                                         sqrtf(s_imu_bias.bias_ay * s_imu_bias.bias_ay
                                             + s_imu_bias.bias_az * s_imu_bias.bias_az));
        s_imu_conditioner.attitude_initialized = true;
    }
#endif

#if TEST_UKF_DISTANCE_ZERO_SIMULATION
    ukf.initialized = true;
#endif

    return SYS_SENSOR_FUSION_OK;
}

sys_sensor_fusion_err_t sys_sensor_fusion_predict(sys_sensor_fusion_data_t *p_ukf)
{
	CHECK_ERR(p_ukf != NULL, SYS_SENSOR_FUSION_ERR);

    if (ukf.initialized && ukf.last_update_tick != 0U)
    {
        if (HAL_GetTick() - ukf.last_update_tick > SYS_FUSION_PREDICT_TIMEOUT_MS)
        {
            RLOG_W(LOG_OBJECT_CODE_TAG, "[FUSION] Predict timeout (> %u ms) without update. Disabling predict.", SYS_FUSION_PREDICT_TIMEOUT_MS);
            sys_sensor_fusion_clear_predict_flag();
            return SYS_SENSOR_FUSION_OK;
        }
    }

    if (g_imu_data_queue == NULL) {
        return SYS_SENSOR_FUSION_OK;
    }

    bsp_imu_data_t temp_imu;
    bool has_imu = false;
    while (osMessageQueueGet(g_imu_data_queue, &temp_imu, NULL, 0U) == osOK) {
        // Chuyển đổi hệ tọa độ
        ukf.imu_current.ax = -temp_imu.ax;
        ukf.imu_current.ay = -temp_imu.ay;
        ukf.imu_current.gz = temp_imu.gz;
        ukf.imu_current.az = temp_imu.az;
        ukf.imu_current.gx = -temp_imu.gx;
        ukf.imu_current.gy = -temp_imu.gy;
        ukf.imu_current.gz = temp_imu.gz;
//        ukf.imu_current = temp_imu;
        has_imu = true;
    }

    if (!has_imu) {
        return SYS_SENSOR_FUSION_OK;
    }

#if SYS_FUSION_DIAGNOSTIC_DISABLE_PREDICT
    return SYS_SENSOR_FUSION_OK;
#endif

    uint32_t sys_predict_tick_ms = HAL_GetTick();
    float dt = calc_dt();
    s_fusion_dt = dt;

#if ENABLE_SYS_FUSION
	sys_predict_count++;

    bsp_imu_data_t imu_raw = ukf.imu_current;
    ukf.imu_current = condition_imu_sample(&imu_raw, dt);

	/* On the first frame imu_old is still zero-initialized; pair it with the
	 * current sample so the trapezoidal integration below does not integrate
	 * against a bogus zero (which corrupts the very first yaw/motion step). */
	if (ukf.is_first_frame)
	{
		ukf.imu_old = ukf.imu_current;
	}

	yaw += (0.5f * (ukf.imu_old.gz + ukf.imu_current.gz) - b_gz_t) * dt;

	if (ukf.is_first_frame)
	{
		static float32_t P_aug[N * N];
		static float32_t L_aug[N * N];
		static arm_matrix_instance_f32 mat_Paug, mat_Laug;
		
		memset(P_aug, 0, sizeof(P_aug));
		memset(L_aug, 0, sizeof(L_aug));
		
		arm_mat_init_f32(&mat_Paug, N, N, P_aug);
		arm_mat_init_f32(&mat_Laug, N, N, L_aug);

        // P_aug 	= [P 0 	0]
		// 			= [0 Qa 0]
		// 			= [0 0 	Qg]
		for(int i=0; i<NUM_STATE; i++)
		{
			for(int j=0; j<NUM_STATE; j++) P_aug[i*N + j] = ukf.P_data[i*NUM_STATE + j];
		}
		for(int i=0; i<NUM_PREDICT_NOISE; i++)
		{
			for(int j=0; j<NUM_PREDICT_NOISE; j++) P_aug[(NUM_STATE+i)*N + (NUM_STATE+j)] = ukf.Q_data[i*NUM_PREDICT_NOISE + j];
		}

        // L_aug = chol(P_aug)
		arm_status status = arm_mat_cholesky_f32(&mat_Paug, &mat_Laug);
		if(status != ARM_MATH_SUCCESS)
        {
            sys_predict_err_count++;
            return SYS_SENSOR_FUSION_ERR;
        }

        // L_aug *= GAMMA_N
		for(int i=0; i<N*N; i++) L_aug[i] *= GAMMA_N;

        // x_aug = [state; 0; 0; 0]
		float32_t x_aug[N] = {
			ukf.state.px, ukf.state.py, ukf.state.vx, ukf.state.vy, ukf.state.theta,
			ukf.state.b_ax, ukf.state.b_ay, ukf.state.b_gz,
			0, 0, 0 // noise IMU
		};

        // 	if(m==0): 		x_sigma = x_aug
		//  else if(m<=N): 	x_sigma = x_aug + L_aug
		//  else: 			x_sigma = x_aug - L_aug
		for(int m = 0; m < NUM_PREDICT_SIGMA; m++)
		{
			float32_t x_sigma[N];
			if (m == 0)
			{
				for(int i=0; i<N; i++) x_sigma[i] = x_aug[i];
			}
			else if (m <= N)
			{
				for(int i=0; i<N; i++) x_sigma[i] = x_aug[i] + L_aug[i*N + (m-1)];
			}
			else
			{
				for(int i=0; i<N; i++) x_sigma[i] = x_aug[i] - L_aug[i*N + (m-1-N)];
			}

			//	X_sigma_pred = first 8 states (px,py,vx,vy,θ,bax,bay,bgz)
			//  Noise_sigma_pred = last 3 states (n_ax, n_ay, n_gz) = process noise samples
			for(int i=0; i<NUM_STATE; i++) ukf.X_sigma_pred[i][m] = x_sigma[i];
			for(int i=0; i<NUM_PREDICT_NOISE; i++) ukf.Noise_sigma_pred[i][m] = x_sigma[NUM_STATE+i];
		}
		/* NOTE */
		ukf.is_first_frame = false; // Đã tạo xong, các vòng IMU tiếp theo sẽ bỏ qua khối lệnh này
	}

	// LUÔN LUÔN CHẠY: Truyền các điểm Sigma ĐÃ LƯU qua mô hình động học
    apply_zupt_velocity_constraint();

	for(int m = 0; m < NUM_PREDICT_SIGMA; m++)
	{
		float px = ukf.X_sigma_pred[0][m], py = ukf.X_sigma_pred[1][m];
		float vx = ukf.X_sigma_pred[2][m], vy = ukf.X_sigma_pred[3][m];
		float theta = ukf.X_sigma_pred[4][m];
		float bax = ukf.X_sigma_pred[5][m], bay = ukf.X_sigma_pred[6][m], bgz = ukf.X_sigma_pred[7][m];

		float n_ax = ukf.Noise_sigma_pred[0][m], n_ay = ukf.Noise_sigma_pred[1][m], n_gz = ukf.Noise_sigma_pred[2][m];

		float w_avg = 0.5f * (ukf.imu_old.gz + ukf.imu_current.gz) - bgz + n_gz;
		float theta_new = theta + w_avg * dt;

		float ax_old = (ukf.imu_old.ax - bax + n_ax)*cosf(theta) - (ukf.imu_old.ay - bay + n_ay)*sinf(theta);
		float ay_old = (ukf.imu_old.ax - bax + n_ax)*sinf(theta) + (ukf.imu_old.ay - bay + n_ay)*cosf(theta);

		float ax_new = (ukf.imu_current.ax - bax + n_ax)*cosf(theta_new) - (ukf.imu_current.ay - bay + n_ay)*sinf(theta_new);
		float ay_new = (ukf.imu_current.ax - bax + n_ax)*sinf(theta_new) + (ukf.imu_current.ay - bay + n_ay)*cosf(theta_new);

		float ax_avg = 0.5f * (ax_old + ax_new);
		float ay_avg = 0.5f * (ay_old + ay_new);

		// Cập nhật đè lên chính nó để tích phân tiếp cho vòng IMU sau
		ukf.X_sigma_pred[0][m] = px + vx*dt + 0.5f*ax_avg*dt*dt;
		ukf.X_sigma_pred[1][m] = py + vy*dt + 0.5f*ay_avg*dt*dt;
		ukf.X_sigma_pred[2][m] = vx + ax_avg*dt;
		ukf.X_sigma_pred[3][m] = vy + ay_avg*dt;
		ukf.X_sigma_pred[4][m] = theta_new;
		// Bias không đổi
	}

	// X̄_k = Σ ω_m^{(n)}·X̂_{k,n}
	float32_t x_mean[NUM_STATE] = {0};
	for(int m=0; m<NUM_PREDICT_SIGMA; m++)
	{
		for(int i=0; i<NUM_STATE; i++) x_mean[i] += ukf.Wm_N[m] * ukf.X_sigma_pred[i][m];
	}

    // Theory: P̄_k = Σ ω_c^{(n)}·(X̂_{k,n} - X̄_k)(X̂_{k,n} - X̄_k)ᵀ  (weighted covariance)
	// Code: diff[i] = X_sigma_pred[i][m] - x_mean[i]
	//       P_data += Wc_N[m] * diff[i] * diff[j]
	for(int i=0; i<NUM_STATE*NUM_STATE; i++) ukf.P_data[i] = 0.0f;
	for(int m=0; m<NUM_PREDICT_SIGMA; m++)
	{
		float32_t diff[NUM_STATE];
		for(int i=0; i<NUM_STATE; i++) diff[i] = ukf.X_sigma_pred[i][m] - x_mean[i];
		diff[4] = normalize_angle(diff[4]);

		for(int i=0; i<NUM_STATE; i++)
		{
			for(int j=0; j<NUM_STATE; j++)
			{
				ukf.P_data[i*NUM_STATE + j] += ukf.Wc_N[m] * diff[i] * diff[j];
			}
		}
	}

	// Cập nhật State
#if SYS_FUSION_IMU_ZUPT_ENABLE
    if (s_imu_conditioner.zupt_active)
    {
        for (int i = 0; i < NUM_STATE; i++)
        {
            ukf.P_data[2 * NUM_STATE + i] = 0.0f;
            ukf.P_data[i * NUM_STATE + 2] = 0.0f;
            ukf.P_data[3 * NUM_STATE + i] = 0.0f;
            ukf.P_data[i * NUM_STATE + 3] = 0.0f;
        }
        ukf.P_data[2 * NUM_STATE + 2] = SYS_FUSION_IMU_ZUPT_VEL_VARIANCE;
        ukf.P_data[3 * NUM_STATE + 3] = SYS_FUSION_IMU_ZUPT_VEL_VARIANCE;
    }
#endif

	ukf.state.px = x_mean[0]; ukf.state.py = x_mean[1];
	ukf.state.vx = x_mean[2]; ukf.state.vy = x_mean[3];
	ukf.state.theta = normalize_angle(x_mean[4]);
	ukf.state.b_ax = x_mean[5]; ukf.state.b_ay = x_mean[6]; ukf.state.b_gz = x_mean[7];

	ukf.imu_old = ukf.imu_current;

	if (p_ukf != NULL) *p_ukf = ukf.state;

#endif

    sys_sensor_fusion_stream_uart(UKF_STEP_PREDICT);
    predict_delta_ms = HAL_GetTick() - sys_predict_tick_ms;

	return SYS_SENSOR_FUSION_OK;
}

sys_sensor_fusion_err_t sys_sensor_fusion_set_initial_position(sys_sensor_fusion_data_t *p_ukf, float x0, float y0)
{
	ukf.state.px = x0;
	ukf.state.py = y0;
	if (p_ukf != NULL) *p_ukf = ukf.state;
	return SYS_SENSOR_FUSION_OK;
}

sys_sensor_fusion_err_t sys_sensor_fusion_realign_position(sys_sensor_fusion_data_t *p_ukf, float x0, float y0)
{
	ukf.state.px = x0;
	ukf.state.py = y0;
	ukf.state.vx = 0.0f;
	ukf.state.vy = 0.0f;
	/* Inflate position covariance to allow rapid filter re-adaptation */
	ukf.P_data[0U * NUM_STATE + 0U] = 0.25f;
	ukf.P_data[0U * NUM_STATE + 1U] = 0.0f;
	ukf.P_data[1U * NUM_STATE + 0U] = 0.0f;
	ukf.P_data[1U * NUM_STATE + 1U] = 0.25f;
	ukf.last_update_tick = HAL_GetTick();
	sys_sensor_fusion_set_predict_flag();
	if (p_ukf != NULL) *p_ukf = ukf.state;
	return SYS_SENSOR_FUSION_OK;
}

bool sys_sensor_fusion_is_initialized(void)
{
    return ukf.initialized;
}

bool sys_sensor_fusion_get_position_covariance(float *pxx, float *pxy, float *pyy)
{
    if (!ukf.initialized || !pxx || !pxy || !pyy) {
        return false;
    }

    const float p00 = ukf.P_data[0U * NUM_STATE + 0U];
    const float p01 = 0.5f * (ukf.P_data[0U * NUM_STATE + 1U]
                            + ukf.P_data[1U * NUM_STATE + 0U]);
    const float p11 = ukf.P_data[1U * NUM_STATE + 1U];
    const float determinant = p00 * p11 - p01 * p01;
    const float determinant_tolerance =
        1.0e-6f * fmaxf(1.0f, fabsf(p00 * p11));
    if (!isfinite(p00) || !isfinite(p01) || !isfinite(p11)
        || !isfinite(determinant)
        || p00 < 0.0f || p11 < 0.0f
        || determinant < -determinant_tolerance) {
        return false;
    }

    *pxx = p00;
    *pxy = p01;
    *pyy = p11;
    return true;
}

static bool get_anchor_slot(uint8_t aid, uint8_t *slot_out)
{
    if (!slot_out) {
        return false;
    }

    const sys_config_t *cfg = sys_config_get();
    uint32_t count = (cfg->anchor_count > NUM_ANCHORS) ? NUM_ANCHORS : cfg->anchor_count;
    for (uint32_t i = 0U; i < count; i++) {
        if (cfg->anchor_layout[i].anchor_id == aid) {
            *slot_out = (uint8_t)i;
            return true;
        }
    }
    return false;
}

bool sys_sensor_fusion_update(sys_sensor_fusion_data_t *p_ukf,
							  const vec2d_t *tril_position,
							  const mw_tril_anchor_t selected_anchors[3],
							  const mw_tril_anchor_t *candidate_anchors,
							  uint8_t candidate_count,
							  uint8_t selected_anchor_mask,
							  const uwb_distance_msg_t *ranging_msg)
{
    CHECK_ERR(p_ukf && tril_position && selected_anchors && candidate_anchors, false);

    s_last_selected_anchors_mask = selected_anchor_mask;
    s_latest_tril_x = (float)tril_position->x;
    s_latest_tril_y = (float)tril_position->y;

    if (!ukf.initialized)
    {
        float init_x, init_y;
        float init_d0, init_d1, init_d2;
        bool pos_done = mw_filter_ukf_init_add(&s_ukf_init_filter,
                                               (float)tril_position->x,
                                               (float)tril_position->y,
                                               &init_x,
                                               &init_y);
        bool dist_done = mw_filter_ukf_init_distance_add(&s_ukf_init_dist_filter,
                                                         (float)selected_anchors[0].distance,
                                                         (float)selected_anchors[1].distance,
                                                         (float)selected_anchors[2].distance,
                                                         &init_d0,
                                                         &init_d1,
                                                         &init_d2);

        if (!pos_done || !dist_done) {
            return false;
        }

        ukf.initialized = true;
        RLOG_I(LOG_OBJECT_CODE_TAG, "[FUSION UKF Init] Tril Px=%.3fm Py=%.3fm Z=%.2fm",
               init_x, init_y, TAG_HEIGHT_M);

        clear_latest_anchor_metrics();
        const float init_distances[3] = {init_d0, init_d1, init_d2};
        for (uint8_t k = 0U; k < 3U; k++) {
            uint8_t layout_idx = 0U;
            if (active_anchor_index_for_id(selected_anchors[k].id, &layout_idx)) {
                s_latest_distances[layout_idx] = init_distances[k];
            }
        }

        snapshot_latest_anchor_metrics(candidate_anchors, candidate_count);
        update_latest_anchor_data_snapshot(ranging_msg, selected_anchors);

        sys_sensor_fusion_set_initial_position(p_ukf, init_x, init_y);
        sys_sensor_fusion_set_predict_flag();
        ukf.last_update_tick = HAL_GetTick();
       ukf.state.theta = yaw_rad_cached;
       yaw             = yaw_rad_cached;
        return true;
    }

    clear_latest_anchor_metrics();
    for (uint8_t k = 0; k < candidate_count; k++) {
        uint8_t aid = candidate_anchors[k].id;
        uint8_t layout_idx = 0U;
        if (active_anchor_index_for_id(aid, &layout_idx)) {
            s_latest_distances[layout_idx] = (float)candidate_anchors[k].distance;
        }
    }

    snapshot_latest_anchor_metrics(candidate_anchors, candidate_count);
    update_latest_anchor_data_snapshot(ranging_msg, selected_anchors);

#if SYS_FUSION_DIAGNOSTIC_USE_TRIL_POSITION
    ukf.state.px = (float)tril_position->x;
    ukf.state.py = (float)tril_position->y;
    ukf.state.vx = 0.0f;
    ukf.state.vy = 0.0f;
    *p_ukf = ukf.state;
    ukf.last_update_tick = HAL_GetTick();
    sys_sensor_fusion_set_predict_flag();
    sys_sensor_fusion_stream_uart(UKF_STEP_UPDATE);
    return true;
#endif

    const uint8_t selected_anchor_ids[3] = {
        selected_anchors[0].id,
        selected_anchors[1].id,
        selected_anchors[2].id
    };

#if SYS_FUSION_DIAGNOSTIC_UPDATE_PACKET
    s_update_diagnostic.valid = false;
    s_update_diagnostic.tril_x = (float)tril_position->x;
    s_update_diagnostic.tril_y = (float)tril_position->y;
    memcpy(s_update_diagnostic.anchor_ids,
           selected_anchor_ids,
           sizeof(s_update_diagnostic.anchor_ids));
#endif

    /* measurement_weight is a precision (1 / variance). Keep the UKF update
     * numerically bounded, and never give a rescued range normal confidence. */
    for (uint8_t k = 0U; k < 3U; k++) {
        float r_ii = MW_UKF_R_MAX;
        double weight = selected_anchors[k].measurement_weight;
        if (!selected_anchors[k].rescued && weight > 0.0 && isfinite(weight)) {
            r_ii = (float)(1.0 / weight);
            if (r_ii < MW_UKF_R_MIN) r_ii = MW_UKF_R_MIN;
            if (r_ii > MW_UKF_R_MAX) r_ii = MW_UKF_R_MAX;
        }
        ukf.R_data[k * (NUM_UPDATE_NOISE + 1U)] = r_ii;
    }

    if (fusion_update( p_ukf,
                        (float)selected_anchors[0].distance,
                        (float)selected_anchors[1].distance,
                        (float)selected_anchors[2].distance,
                        selected_anchor_ids) != SYS_SENSOR_FUSION_OK) {
        return false;
    }

    ukf.last_update_tick = HAL_GetTick();
    sys_sensor_fusion_set_predict_flag();

    sys_sensor_fusion_stream_uart(UKF_STEP_UPDATE);

    return true;
}

void sys_sensor_fusion_report_error(void)
{
    s_error_count++;
}

void sys_sensor_fusion_clear_latest_anchor_metrics(void)
{
    clear_latest_anchor_metrics();
}

void sys_sensor_fusion_reset_error(void)
{
    s_error_count = 0U;
    s_latest_ranging_error_count = 0U;
    s_prefilter_reject_count = 0U;
}

uint32_t sys_sensor_fusion_get_error_count(void)
{
    return s_error_count;
}

void sys_sensor_fusion_reset(void)
{
    RLOG_I(LOG_OBJECT_CODE_TAG, "[FUSION] Resetting sensor fusion filters and state from thread...");
    sys_sensor_fusion_clear_predict_flag();
    sys_sensor_fusion_clear_update_flag();
    s_error_count = 0U;
    sys_sensor_fusion_data_t reset_state = {0};
    if (sys_sensor_fusion_init(&reset_state) != SYS_SENSOR_FUSION_OK)
    {
        RLOG_W(LOG_OBJECT_CODE_TAG, "[FUSION] UKF re-initialization failed");
    }
    else
    {
        RLOG_I(LOG_OBJECT_CODE_TAG, "[FUSION] UKF re-initialized successfully");
    }
}

void sys_sensor_fusion_stream_test_init(network_core_t *stream)
{
#if TEST_UKF_STREAM_BLE && ENABLE_SYS_FUSION
    CHECK_VOID(stream);
    s_stream_test_sample_idx = 0U;
#if TEST_UKF_STREAM_FUSION_LOG
    s_stream_test_tx_frame_cnt = 0U;
#endif
    configure_adv(stream);
#else
    (void)stream;
#endif
}
protobuf_sensor_fusion_result_t stream_data;
void sys_sensor_fusion_stream_ble(uint8_t ukf_step)
{
#if TEST_UKF_STREAM_BLE && ENABLE_SYS_FUSION

    uint32_t now_ms = HAL_GetTick();

    protobuf_sensor_fusion_result_t stream_data;
    memset(&stream_data, 0, sizeof(stream_data));
    stream_data.ukf_step = ukf_step;

    const float start_x = 1.0f;
    const float end_x   = 3.0f;
    const float start_y = 1.0f;
    const float end_y   = 3.0f;
    const float step_m  = 0.05f;

    uint32_t points_per_row = (uint32_t)((end_x - start_x) / step_m) + 1U;
    uint32_t row_count      = (uint32_t)((end_y - start_y) / step_m) + 1U;
    uint32_t total_points   = points_per_row * row_count;

    uint32_t idx = s_stream_test_sample_idx % total_points;
    uint32_t row = idx / points_per_row;
    uint32_t col = idx % points_per_row;

    float x;
    float y = start_y + ((float)row * step_m);

    if ((row % 2U) == 0U)
    {
        x = start_x + ((float)col * step_m);   // hàng chẵn: đi sang phải
        stream_data.ukf_yaw_deg = 0;
    }
    else
    {
        x = end_x - ((float)col * step_m);     // hàng lẻ: đi sang trái
        stream_data.ukf_yaw_deg = to_proto_fixed2(180.0f);
    }

    stream_data.ukf_x_m = to_proto_fixed2(x);
    stream_data.ukf_y_m = to_proto_fixed2(y);

    /* Trilateration giả lập lệch nhẹ so với UKF */
    stream_data.tril_x_m = to_proto_fixed2(x + 0.05f);
    stream_data.tril_y_m = to_proto_fixed2(y - 0.05f);
    stream_data.yaw_deg  = stream_data.ukf_yaw_deg;

    const uint8_t anchor_mask =
        (uint8_t)((s_stream_test_sample_idx / TEST_UKF_STREAM_MASK_PACKET_COUNT) & 0x0FU);
    static const float anchor_positions[TEST_UKF_STREAM_ANCHOR_COUNT][2] = {
        {0.0f, 0.0f},
        {4.0f, 0.0f},
        {0.0f, 4.0f},
        {4.0f, 4.0f},
    };

    stream_data.anchor_mask = anchor_mask;
    stream_data.ranging_error_count = s_stream_test_sample_idx;
    stream_data.timestamp_ms = now_ms;
    stream_data.zone_id = 0U;
    stream_data.anchors_count = TEST_UKF_STREAM_ANCHOR_COUNT;
    for (uint32_t i = 0U; i < TEST_UKF_STREAM_ANCHOR_COUNT; i++)
    {
        const float dx = x - anchor_positions[i][0];
        const float dy = y - anchor_positions[i][1];
        protobuf_anchor_data_t *anchor = &stream_data.anchors[i];

        anchor->anchor_id = i + 1U;
        anchor->distance_mm = (uint32_t)(sqrtf(dx * dx + dy * dy) * 1000.0f);
        anchor->weight = ((anchor_mask & (1U << i)) != 0U) ? 100 : 0;
    }

#if TEST_UKF_STREAM_FUSION_LOG
    protobuf_calib_data_t calib_data;
    memset(&calib_data, 0, sizeof(calib_data));
    const float imu_phase = (float)s_stream_test_sample_idx * 0.05f;

    calib_data.anchor_mask = anchor_mask;
    calib_data.tx_frame_cnt = s_stream_test_tx_frame_cnt;
    calib_data.ax = 0.25f * sinf(imu_phase);
    calib_data.ay = 0.20f * cosf(imu_phase);
    calib_data.gz = 0.10f * sinf(imu_phase * 0.5f);
    calib_data.px = x;
    calib_data.py = y;
    calib_data.distance_count = TEST_UKF_STREAM_ANCHOR_COUNT;
    calib_data.fp_amp_norm_count = TEST_UKF_STREAM_ANCHOR_COUNT;
    calib_data.fp_snr_count = TEST_UKF_STREAM_ANCHOR_COUNT;
    calib_data.error_frame_cnt = 0U;
    calib_data.dt = 0.02f;

    for (uint32_t i = 0U; i < TEST_UKF_STREAM_ANCHOR_COUNT; i++)
    {
        calib_data.distance[i] = (float)stream_data.anchors[i].distance_mm / 1000.0f;
        calib_data.fp_amp_norm[i] = 1.0;
        calib_data.fp_snr[i] = 20.0;
    }

    if (network_send_calib_data(&g_network_core,
                                protobuf_PACKET_ADDR_HOST,
                                &calib_data))
    {
        s_stream_test_tx_frame_cnt++;
        s_stream_test_sample_idx++;
    }
#else
    if (network_send_sensor_fusion_result(&g_network_core, protobuf_PACKET_ADDR_HOST, &stream_data))
    {
        s_stream_test_sample_idx++;
    }
#endif
#else
#if ENABLE_SYS_FUSION
    if (!ukf.initialized)
    {
        return;
    }
#endif

#if ENABLE_SYS_FUSION
    const sys_config_t *cfg = sys_config_get();

    memset(&stream_data, 0, sizeof(stream_data));

#if SYS_FUSION_DIAGNOSTIC_UPDATE_PACKET
    /* In diagnostic mode, suppress ordinary predict/update telemetry. Predict
     * calls still arrive because the disabled predictor returns OK, and those
     * packets would otherwise consume the shared 20 ms stream rate limit.
     * A pending diagnostic snapshot may be retried by any subsequent call. */
    if (!s_update_diagnostic.valid)
    {
        return;
    }

    {
        const float prior_position_covariance[NUM_UPDATE_NOISE] = {
            s_update_diagnostic.prior_pxx,
            s_update_diagnostic.prior_pxy,
            s_update_diagnostic.prior_pyy
        };

        stream_data.ukf_step = SYS_FUSION_DIAGNOSTIC_UPDATE_STEP;
        /* Diagnostic positions use raw fixed3. Studio's unchanged fixed2 CSV
         * export therefore stores value_m * 10; the dedicated parser divides
         * those CSV fields by 10 to recover meters at millimeter resolution. */
        stream_data.ukf_x_m =
            to_proto_fixed3(s_update_diagnostic.posterior_px);
        stream_data.ukf_y_m =
            to_proto_fixed3(s_update_diagnostic.posterior_py);
        stream_data.ukf_yaw_deg =
            to_proto_fixed3(s_update_diagnostic.prior_px);
        stream_data.tril_x_m =
            to_proto_fixed3(s_update_diagnostic.tril_x);
        stream_data.tril_y_m =
            to_proto_fixed3(s_update_diagnostic.tril_y);
        stream_data.yaw_deg =
            to_proto_fixed3(s_update_diagnostic.prior_py);
        stream_data.anchor_mask = s_last_selected_anchors_mask;
        stream_data.ranging_error_count =
            ((uint32_t)s_update_diagnostic.anchor_ids[0])
          | ((uint32_t)s_update_diagnostic.anchor_ids[1] << 8U)
          | ((uint32_t)s_update_diagnostic.anchor_ids[2] << 16U);
        stream_data.timestamp_ms = HAL_GetTick();
        stream_data.zone_id = cfg ? cfg->default_zone_id : 0U;
        stream_data.prefilter_reject_count = s_prefilter_reject_count;
        stream_data.position_cov_xx_m2 = s_update_diagnostic.prior_pxx;
        stream_data.position_cov_xy_m2 = s_update_diagnostic.prior_pxy;
        stream_data.position_cov_yy_m2 = s_update_diagnostic.prior_pyy;
        stream_data.position_cov_valid =
            isfinite(stream_data.position_cov_xx_m2)
            && isfinite(stream_data.position_cov_xy_m2)
            && isfinite(stream_data.position_cov_yy_m2)
            && stream_data.position_cov_xx_m2 >= 0.0f
            && stream_data.position_cov_yy_m2 >= 0.0f;
        stream_data.anchors_count = 2U * NUM_UPDATE_NOISE;

        for (uint8_t i = 0U; i < NUM_UPDATE_NOISE; i++)
        {
            protobuf_anchor_data_t *measurement = &stream_data.anchors[i];
            protobuf_anchor_data_t *prediction =
                &stream_data.anchors[NUM_UPDATE_NOISE + i];

            measurement->anchor_id = (uint32_t)i + 1U;
            measurement->distance_mm =
                to_mm_u32(s_update_diagnostic.d_real[i]);
            measurement->weight =
                to_scaled_i32(s_update_diagnostic.r_diag[i],
                              SYS_FUSION_DIAGNOSTIC_WEIGHT_SCALE);

            prediction->anchor_id =
                (uint32_t)(NUM_UPDATE_NOISE + i) + 1U;
            prediction->distance_mm =
                to_mm_u32(s_update_diagnostic.d_mean[i]);
            prediction->weight =
                to_scaled_i32(prior_position_covariance[i],
                              SYS_FUSION_DIAGNOSTIC_WEIGHT_SCALE);
        }

        if (network_send_sensor_fusion_result(&g_network_core,
                                              protobuf_PACKET_ADDR_HOST,
                                              &stream_data))
        {
            s_update_diagnostic.valid = false;
        }
        return;
    }
#endif

    stream_data.ukf_step            = ukf_step;
    stream_data.ukf_x_m 			= to_proto_fixed2(ukf.state.px);
    stream_data.ukf_y_m 			= to_proto_fixed2(ukf.state.py);
    stream_data.ukf_yaw_deg 		= to_proto_fixed2(sys_sensor_fusion_get_ukf_yaw_deg());
    stream_data.tril_x_m 			= to_proto_fixed2(s_latest_tril_x);
    stream_data.tril_y_m 			= to_proto_fixed2(s_latest_tril_y);
    stream_data.yaw_deg 			= to_proto_fixed2(sys_sensor_fusion_get_yaw_deg());
    stream_data.anchor_mask 		= s_last_selected_anchors_mask;
    stream_data.ranging_error_count =
        (UINT32_MAX - s_latest_ranging_error_count < s_error_count)
        ? UINT32_MAX
        : (s_latest_ranging_error_count + s_error_count);
    stream_data.timestamp_ms 		= HAL_GetTick();
    stream_data.zone_id 			= cfg ? cfg->default_zone_id : 0U;
    stream_data.prefilter_reject_count = s_prefilter_reject_count;
    stream_data.position_cov_valid =
        sys_sensor_fusion_get_position_covariance(
            &stream_data.position_cov_xx_m2,
            &stream_data.position_cov_xy_m2,
            &stream_data.position_cov_yy_m2);
    stream_data.anchors_count 		= s_latest_anchor_data_count;
    memcpy(stream_data.anchors, s_latest_anchor_data,
    (size_t)s_latest_anchor_data_count * sizeof(stream_data.anchors[0]));

    (void)network_send_sensor_fusion_result(&g_network_core,
                                            protobuf_PACKET_ADDR_HOST,
                                            &stream_data);
#else
    static uint32_t tx_frame_cnt = 0U;
    protobuf_calib_data_t stream_data;
    memset(&stream_data, 0, sizeof(stream_data));

    stream_data.anchor_mask = s_last_selected_anchors_mask;
    stream_data.tx_frame_cnt = tx_frame_cnt;
    stream_data.ax = ukf.imu_current.ax;
    stream_data.ay = ukf.imu_current.ay;
    stream_data.gz = ukf.imu_current.gz;
    stream_data.px = s_latest_tril_x;
    stream_data.py = s_latest_tril_y;
    stream_data.distance_count = NUM_ANCHORS;
    stream_data.fp_amp_norm_count = NUM_ANCHORS;
    stream_data.fp_snr_count = NUM_ANCHORS;
    memcpy(stream_data.distance, s_latest_distances, sizeof(s_latest_distances));
    memcpy(stream_data.fp_amp_norm, s_latest_fp_amp_norm, sizeof(s_latest_fp_amp_norm));
    memcpy(stream_data.fp_snr, s_latest_fp_snr, sizeof(s_latest_fp_snr));
    stream_data.error_frame_cnt = s_error_count;
    stream_data.dt = s_fusion_dt;

    if (network_send_calib_data(&g_network_core,
                                protobuf_PACKET_ADDR_HOST,
                                &stream_data)) {
        tx_frame_cnt++;
    }
#endif
#endif
}

void sys_sensor_fusion_stream_uart(uint8_t ukf_step)
{
#if TEST_UKF_STREAM_UART
    const float start_x = 1.0f;
    const float end_x   = 3.0f;
    const float start_y = 1.0f;
    const float end_y   = 3.0f;
    const float step_m  = 0.05f;

    uint32_t points_per_row = (uint32_t)((end_x - start_x) / step_m) + 1U;
    uint32_t row_count      = (uint32_t)((end_y - start_y) / step_m) + 1U;
    uint32_t total_points   = points_per_row * row_count;

    uint32_t idx = s_stream_test_sample_idx % total_points;
    uint32_t row = idx / points_per_row;
    uint32_t col = idx % points_per_row;

    float x;
    float y = start_y + ((float)row * step_m);
    float ukf_yaw_deg = 0.0f;

    if ((row % 2U) == 0U)
    {
        x = start_x + ((float)col * step_m);   // hàng chẵn: đi sang phải
        ukf_yaw_deg = 0.0f;
    }
    else
    {
        x = end_x - ((float)col * step_m);     // hàng lẻ: đi sang trái
        ukf_yaw_deg = 180.0f;
    }

    if (bsp_io_uart_send_fusion_data(0U,
                                     to_uart_fixed2(x),
                                     to_uart_fixed2(y),
                                     to_uart_fixed2(ukf_yaw_deg),
                                     to_uart_fixed2((x + 0.05f)),
                                     to_uart_fixed2((y + 0.05f)),
                                     to_uart_fixed2(ukf_yaw_deg),
                                     UKF_STEP_PREDICT,
                                     s_error_count) == BSP_OK)
    {
        s_stream_test_sample_idx++;
    }

#else
#if ENABLE_SYS_FUSION
    if (!ukf.initialized) 
    {
        return;
    }
#endif

#if ENABLE_SYS_FUSION
    if(ukf_step == UKF_STEP_PREDICT)
    {
    	float ukf_yaw = sys_sensor_fusion_get_ukf_yaw_deg();
		float raw_yaw = sys_sensor_fusion_get_yaw_deg();

		(void)bsp_io_uart_send_fusion_data(s_last_selected_anchors_mask,
										to_uart_fixed2(ukf.state.px),
										to_uart_fixed2(ukf.state.py),
										to_uart_fixed2(ukf_yaw),
										to_uart_fixed2(s_latest_tril_x),
										to_uart_fixed2(s_latest_tril_y),
										to_uart_fixed2(raw_yaw),
										UKF_STEP_PREDICT,
										s_error_count);
    }
    else if(ukf_step == UKF_STEP_UPDATE)
    {
    	(void)bsp_io_uart_send_fusion_data(s_last_selected_anchors_mask,
    	                                        to_uart_fixed2(ukf.state.px),
    	                                        to_uart_fixed2(ukf.state.py),
    	                                        0,
    	                                        to_uart_fixed2(s_latest_tril_x),
    	                                        to_uart_fixed2(s_latest_tril_y),
    	                                        0,
    	                                        UKF_STEP_UPDATE,
    	                                        s_error_count);
    }

#else
    bsp_io_uart_send_fusion_log_data(s_last_selected_anchors_mask,
                                         s_error_count,
										 ukf.imu_current.ax,
										 ukf.imu_current.ay,
										 ukf.imu_current.gz,
                                         (float)s_latest_tril_x,
                                         (float)s_latest_tril_y,
                                         s_latest_distances,
                                         s_latest_fp_amp_norm,
                                         s_latest_fp_snr,
                                         s_fusion_dt);
#endif
#endif
}

sys_sensor_fusion_err_t sys_sensor_fusion_set_update_flag()
{
	ukf.enable_update = true;
	return SYS_SENSOR_FUSION_OK;
}

sys_sensor_fusion_err_t sys_sensor_fusion_clear_update_flag()
{
	ukf.enable_update = false;
	return SYS_SENSOR_FUSION_OK;
}

sys_sensor_fusion_err_t sys_sensor_fusion_set_predict_flag()
{
	ukf.enable_predict = true;
	return SYS_SENSOR_FUSION_OK;
}

sys_sensor_fusion_err_t sys_sensor_fusion_clear_predict_flag()
{
	ukf.enable_predict = false;
	return SYS_SENSOR_FUSION_OK;
}

bool sys_sensor_fusion_check_update_flag()
{
	return ukf.enable_update;
}

bool sys_sensor_fusion_check_predict_flag()
{
	return ukf.enable_predict;
}

float sys_sensor_fusion_get_ukf_yaw_deg()
{
	return ukf.state.theta * RAD2DEG;
}

float sys_sensor_fusion_get_yaw_deg()
{
	return yaw * RAD2DEG;
}

void sys_sensor_fusion_task()
{
    bsp_imu_data_t imu_data = {0};
    if (bsp_imu_get_raw_data(&imu_data) == BSP_IMU_OK) 
    {
#if ENABLE_SYS_FUSION
        if (g_imu_data_queue == NULL)
        {
            return;
        }

        if (ukf.initialized && ukf.enable_predict)
        {
            (void)osMessageQueuePut(g_imu_data_queue, &imu_data, 0U, 0U);
        }
#else
        /* Preserve the same board-to-navigation axis mapping used by the UKF,
         * but keep this as raw telemetry only when MCU fusion is disabled. */
        ukf.imu_current.ax = -imu_data.ax;
        ukf.imu_current.ay = -imu_data.ay;
        ukf.imu_current.gz = imu_data.gz;
        s_fusion_dt = calc_dt();
#endif
    }
}

void sys_sensor_fusion_set_initial_yaw(uint32_t yaw_deg)
{
    yaw_rad_cached   = (float)(yaw_deg) * DEG2RAD;
}

/* Private definitions ------------------------------------------------ */
sys_sensor_fusion_err_t fusion_update(sys_sensor_fusion_data_t *p_ukf,
                                                 float d0,
                                                 float d1,
                                                 float d2,
                                                 const uint8_t anchor_ids[3])
{
	
#if !ENABLE_SYS_FUSION
	return SYS_SENSOR_FUSION_OK;
#else

    CHECK_ERR(p_ukf != NULL, SYS_SENSOR_FUSION_ERR);
	CHECK_ERR(anchor_ids != NULL, SYS_SENSOR_FUSION_ERR);

    uint32_t sys_update_tick_ms = HAL_GetTick();
	sys_update_count++;

    static float32_t P_aug[M * M];
    static float32_t L_aug[M * M];
    static arm_matrix_instance_f32 mat_Paug, mat_Laug;
    
    memset(P_aug, 0, sizeof(P_aug));
    memset(L_aug, 0, sizeof(L_aug));
    
    arm_mat_init_f32(&mat_Paug, M, M, P_aug);
    arm_mat_init_f32(&mat_Laug, M, M, L_aug);

    // P_aug 	= [P 0]
	// 			= [0 R]
    for(int i=0; i<NUM_STATE; i++)
    {
        for(int j=0; j<NUM_STATE; j++) P_aug[i*M + j] = ukf.P_data[i*NUM_STATE + j];
    }
    for(int i=0; i<NUM_UPDATE_NOISE; i++)
    {
        for(int j=0; j<NUM_UPDATE_NOISE; j++) P_aug[(NUM_STATE+i)*M + (NUM_STATE+j)] = ukf.R_data[i*NUM_UPDATE_NOISE + j];
    }

    // L_aug = chol(P_aug)
    arm_status status = arm_mat_cholesky_f32(&mat_Paug, &mat_Laug);
    if(status != ARM_MATH_SUCCESS)
    {
        sys_update_err_count++;
        sys_update_cholesky_err_count++;
        return SYS_SENSOR_FUSION_ERR;
    }

    // L_aug *= GAMMA_M
    for(int i=0; i<M*M; i++) L_aug[i] *= GAMMA_M;

    static float32_t X_sigma[NUM_STATE][NUM_UPDATE_SIGMA];
    static float32_t D_sigma[NUM_UPDATE_NOISE][NUM_UPDATE_SIGMA];
    
    memset(X_sigma, 0, sizeof(X_sigma));
    memset(D_sigma, 0, sizeof(D_sigma));

    float32_t x_aug[M] = {
        ukf.state.px, ukf.state.py, ukf.state.vx, ukf.state.vy, ukf.state.theta,
        ukf.state.b_ax, ukf.state.b_ay, ukf.state.b_gz,
        0, 0, 0
    };

    float selected_anchor_pos[NUM_UPDATE_NOISE][2] = {0};
    const sys_config_t *cfg = sys_config_get();
    for (uint8_t selected = 0U; selected < NUM_UPDATE_NOISE; selected++) {
        bool found = false;
        for (uint32_t i = 0U; i < cfg->anchor_count; i++) {
            if (cfg->anchor_layout[i].anchor_id == anchor_ids[selected]) {
                selected_anchor_pos[selected][0] = cfg->anchor_layout[i].x_m;
                selected_anchor_pos[selected][1] = cfg->anchor_layout[i].y_m;
                found = true;
                break;
            }
        }
        CHECK_ERR(found, SYS_SENSOR_FUSION_ERR);
    }

    // if(m==0): 		x_s = x_aug
	// else if(m<=M): 	x_s = x_aug + L_aug
	// else: 			x_s = x_aug - L_aug
    for(int m = 0; m < NUM_UPDATE_SIGMA; m++)
    {
        float32_t x_s[M];
        if (m == 0)
        {
            for(int i=0; i<M; i++) x_s[i] = x_aug[i];
        }
        else if (m <= M)
        {
            for(int i=0; i<M; i++) x_s[i] = x_aug[i] + L_aug[i*M + (m-1)];
        }
        else
        {
            for(int i=0; i<M; i++) x_s[i] = x_aug[i] - L_aug[i*M + (m-1-M)];
        }

        for(int i=0; i<NUM_STATE; i++) X_sigma[i][m] = x_s[i];

        // D_sigma[0][m] = sqrt((px-A1x)²+(py-A1y)²) + x_s[8] (noise term)
        float px = x_s[0], py = x_s[1];
        for (uint8_t d_index = 0U; d_index < NUM_UPDATE_NOISE; d_index++) {
            float dx = px - selected_anchor_pos[d_index][0];
            float dy = py - selected_anchor_pos[d_index][1];
            D_sigma[d_index][m] = sqrtf(dx * dx + dy * dy) + x_s[8 + d_index];
        }
    }

    // d_mean[i] = Σ Wm_M[m] * D_sigma[i][m]
    float32_t d_mean[NUM_UPDATE_NOISE] = {0};
    for(int m=0; m<NUM_UPDATE_SIGMA; m++)
    {
        for(int i=0; i<NUM_UPDATE_NOISE; i++) d_mean[i] += ukf.Wm_M[m] * D_sigma[i][m];
    }

    // P_dd += Wc_M[m] * diff_d * diff_dᵀ
    // P_xd += Wc_M[m] * diff_x * diff_dᵀ
    static float32_t P_dd[NUM_UPDATE_NOISE * NUM_UPDATE_NOISE];
    static float32_t P_xd[NUM_STATE * NUM_UPDATE_NOISE];
    memset(P_dd, 0, sizeof(P_dd));
    memset(P_xd, 0, sizeof(P_xd));

    for(int m=0; m<NUM_UPDATE_SIGMA; m++)
    {
        float32_t diff_d[NUM_UPDATE_NOISE], diff_x[NUM_STATE];
        for(int i=0; i<NUM_UPDATE_NOISE; i++) diff_d[i] = D_sigma[i][m] - d_mean[i];
        for(int i=0; i<NUM_STATE; i++) diff_x[i] = X_sigma[i][m] - x_aug[i];
        diff_x[4] = normalize_angle(diff_x[4]);

        for(int i=0; i<NUM_UPDATE_NOISE; i++)
        {
            for(int j=0; j<NUM_UPDATE_NOISE; j++) P_dd[i*NUM_UPDATE_NOISE + j] += ukf.Wc_M[m] * diff_d[i] * diff_d[j];
        }

        for(int i=0; i<NUM_STATE; i++)
        {
            for(int j=0; j<NUM_UPDATE_NOISE; j++) P_xd[i*NUM_UPDATE_NOISE + j] += ukf.Wc_M[m] * diff_x[i] * diff_d[j];
        }
    }

    static float32_t P_dd_inv[NUM_UPDATE_NOISE * NUM_UPDATE_NOISE];
    static float32_t K_data[NUM_STATE * NUM_UPDATE_NOISE];
    static arm_matrix_instance_f32 mat_Pdd_inv, mat_Pxd, mat_K;
    memset(P_dd_inv, 0, sizeof(P_dd_inv));
    memset(K_data, 0, sizeof(K_data));
    arm_mat_init_f32(&mat_Pdd_inv, NUM_UPDATE_NOISE, NUM_UPDATE_NOISE, P_dd_inv);
    arm_mat_init_f32(&mat_Pxd, NUM_STATE, NUM_UPDATE_NOISE, P_xd);
    arm_mat_init_f32(&mat_K, NUM_STATE, NUM_UPDATE_NOISE, K_data);

    if (!invert_innovation_covariance(P_dd, P_dd_inv))
    {
        sys_update_err_count++;
        sys_update_inverse_err_count++;
        return SYS_SENSOR_FUSION_ERR;
    }

    arm_mat_mult_f32(&mat_Pxd, &mat_Pdd_inv, &mat_K);

    float32_t D_real[3] = {d0, d1, d2};
#if SYS_FUSION_DIAGNOSTIC_UPDATE_PACKET
    s_update_diagnostic.prior_px = x_aug[0];
    s_update_diagnostic.prior_py = x_aug[1];
    s_update_diagnostic.prior_pxx = ukf.P_data[0U * NUM_STATE + 0U];
    s_update_diagnostic.prior_pxy =
        0.5f * (ukf.P_data[0U * NUM_STATE + 1U]
              + ukf.P_data[1U * NUM_STATE + 0U]);
    s_update_diagnostic.prior_pyy = ukf.P_data[1U * NUM_STATE + 1U];
    for (uint8_t i = 0U; i < NUM_UPDATE_NOISE; i++)
    {
        s_update_diagnostic.d_real[i] = D_real[i];
        s_update_diagnostic.d_mean[i] = d_mean[i];
        s_update_diagnostic.r_diag[i] =
            ukf.R_data[i * NUM_UPDATE_NOISE + i];
    }
#endif

    for(int i=0; i<NUM_STATE; i++)
    {
        float update_val = 0;
        for(int j=0; j<NUM_UPDATE_NOISE; j++)
        {
            update_val += K_data[i*NUM_UPDATE_NOISE + j] * (D_real[j] - d_mean[j]);
        }

        if (i == 0) ukf.state.px += update_val;
        if (i == 1) ukf.state.py += update_val;
        if (i == 2) ukf.state.vx += update_val;
        if (i == 3) ukf.state.vy += update_val;
        if (i == 4) ukf.state.theta = normalize_angle(ukf.state.theta + update_val);
        if (i == 5) ukf.state.b_ax += update_val;
        if (i == 6) ukf.state.b_ay += update_val;
        if (i == 7) ukf.state.b_gz += update_val;
    }

    static float32_t Pxd_t_data[NUM_UPDATE_NOISE * NUM_STATE];
	static float32_t K_Pxd_t_data[NUM_STATE * NUM_STATE];

	static arm_matrix_instance_f32 mat_Pxd_t, mat_K_Pxd_t;
	arm_mat_init_f32(&mat_Pxd_t, NUM_UPDATE_NOISE, NUM_STATE, Pxd_t_data);
	arm_mat_init_f32(&mat_K_Pxd_t, NUM_STATE, NUM_STATE, K_Pxd_t_data);

	// 1. Chuyển vị ma trận Pxd: (P_xd)^T
	arm_mat_trans_f32(&mat_Pxd, &mat_Pxd_t);

	// 2. Nhân K với (P_xd)^T: K * (P_xd)^T
	arm_mat_mult_f32(&mat_K, &mat_Pxd_t, &mat_K_Pxd_t);

	// 3. Cập nhật P: P = P - K * (P_xd)^T
	arm_mat_sub_f32(&ukf.mat_P, &mat_K_Pxd_t, &ukf.mat_P);
    stabilize_state_covariance();

#if SYS_FUSION_DIAGNOSTIC_UPDATE_PACKET
    s_update_diagnostic.posterior_px = ukf.state.px;
    s_update_diagnostic.posterior_py = ukf.state.py;
    s_update_diagnostic.valid = true;
#endif

    if (p_ukf != NULL) *p_ukf = ukf.state;

    ukf.is_first_frame = true;
	update_delta_ms = HAL_GetTick() - sys_update_tick_ms;
	return SYS_SENSOR_FUSION_OK;

#endif

}

static bool invert_innovation_covariance(const float32_t covariance[9],
                                         float32_t inverse[9])
{
    static const float32_t jitter_levels[] = {
        0.0f, 1.0e-6f, 1.0e-5f, 1.0e-4f, MW_UKF_INNOVATION_JITTER_MAX
    };
    float32_t symmetric[9];
    float32_t work[9];
    arm_matrix_instance_f32 mat_work;
    arm_matrix_instance_f32 mat_inverse;

    if (covariance == NULL || inverse == NULL) {
        return false;
    }

    for (uint8_t row = 0U; row < 3U; row++) {
        for (uint8_t col = 0U; col < 3U; col++) {
            float32_t value = 0.5f * (covariance[row * 3U + col]
                                    + covariance[col * 3U + row]);
            if (!isfinite(value)) {
                return false;
            }
            symmetric[row * 3U + col] = value;
        }
    }

    for (uint8_t attempt = 0U;
         attempt < (uint8_t)(sizeof(jitter_levels) / sizeof(jitter_levels[0]));
         attempt++) {
        memcpy(work, symmetric, sizeof(work));
        for (uint8_t diagonal = 0U; diagonal < 3U; diagonal++) {
            work[diagonal * 3U + diagonal] += jitter_levels[attempt];
        }
        memset(inverse, 0, 9U * sizeof(inverse[0]));
        arm_mat_init_f32(&mat_work, 3U, 3U, work);
        arm_mat_init_f32(&mat_inverse, 3U, 3U, inverse);
        if (arm_mat_inverse_f32(&mat_work, &mat_inverse) != ARM_MATH_SUCCESS) {
            continue;
        }

        bool finite = true;
        for (uint8_t index = 0U; index < 9U; index++) {
            if (!isfinite(inverse[index])) {
                finite = false;
                break;
            }
        }
        if (finite) {
            return true;
        }
    }

    return false;
}

static void stabilize_state_covariance(void)
{
    for (uint8_t row = 0U; row < NUM_STATE; row++) {
        for (uint8_t col = (uint8_t)(row + 1U); col < NUM_STATE; col++) {
            float32_t symmetric = 0.5f * (ukf.P_data[row * NUM_STATE + col]
                                        + ukf.P_data[col * NUM_STATE + row]);
            ukf.P_data[row * NUM_STATE + col] = symmetric;
            ukf.P_data[col * NUM_STATE + row] = symmetric;
        }

        float32_t *diagonal = &ukf.P_data[row * NUM_STATE + row];
        if (!isfinite(*diagonal) || *diagonal < MW_UKF_P_DIAGONAL_FLOOR) {
            *diagonal = MW_UKF_P_DIAGONAL_FLOOR;
        }
    }
}

static float calc_dt(void)
{
    uint32_t now = HAL_GetTick();
    float dt = 0.01f;

    if (ukf.has_predict_tick)
    {
        uint32_t dt_ms = now - ukf.last_predict_tick;
        if (dt_ms > 100U) dt_ms = 100U;
        if (dt_ms < 1U) dt_ms = 1U;
        dt = (float)dt_ms / 1000.0f;
    }

    ukf.last_predict_tick = now;
    ukf.has_predict_tick = true;
    return dt;
}

static void reset_imu_conditioner(void)
{
    memset(&s_imu_conditioner, 0, sizeof(s_imu_conditioner));
}

static void reset_biquad_filter(imu_biquad_filter_t *filter, float value)
{
    if (filter == NULL)
    {
        return;
    }

    filter->x1 = value;
    filter->x2 = value;
    filter->y1 = value;
    filter->y2 = value;
}

static float apply_butterworth_2nd_order(imu_biquad_filter_t *filter, float x, float dt)
{
    if (filter == NULL)
    {
        return x;
    }

    float fs = SYS_FUSION_IMU_SAMPLE_RATE_HZ;
    if (dt > 0.0f)
    {
        fs = 1.0f / dt;
    }
    if (fs <= 0.0f)
    {
        return x;
    }

    float margin = SYS_FUSION_IMU_CUTOFF_NYQUIST_MARGIN;
    if (margin <= 0.0f || margin > 0.99f)
    {
        margin = 0.95f;
    }

    const float nyquist = 0.5f * fs;
    float max_cutoff = nyquist * margin;
    if (max_cutoff < 0.01f)
    {
        max_cutoff = 0.01f;
    }

    float cutoff = SYS_FUSION_IMU_BUTTERWORTH_CUTOFF_HZ;
    if (cutoff < 0.01f)
    {
        cutoff = 0.01f;
    }
    if (cutoff > max_cutoff)
    {
        cutoff = max_cutoff;
    }

    const float q = 0.70710678118f;
    const float omega = SYS_SENSOR_FUSION_2PI * cutoff / fs;
    const float sin_omega = sinf(omega);
    const float cos_omega = cosf(omega);
    const float alpha = sin_omega / (2.0f * q);
    const float a0 = 1.0f + alpha;
    const float b0 = ((1.0f - cos_omega) * 0.5f) / a0;
    const float b1 = (1.0f - cos_omega) / a0;
    const float b2 = b0;
    const float a1 = (-2.0f * cos_omega) / a0;
    const float a2 = (1.0f - alpha) / a0;

    const float y = b0 * x + b1 * filter->x1 + b2 * filter->x2
                  - a1 * filter->y1 - a2 * filter->y2;

    filter->x2 = filter->x1;
    filter->x1 = x;
    filter->y2 = filter->y1;
    filter->y1 = y;
    return y;
}

static void compensate_gravity(bsp_imu_data_t *sample, float dt)
{
#if SYS_FUSION_IMU_PREFILTER_ENABLE
    if (sample == NULL)
    {
        return;
    }

    const float ax = sample->ax;
    const float ay = sample->ay;
    const float az = sample->az;
    const float acc_norm = sqrtf(ax * ax + ay * ay + az * az);

    if (!s_imu_conditioner.attitude_initialized)
    {
        if (acc_norm > 0.1f)
        {
            s_imu_conditioner.roll = atan2f(ay, az);
            s_imu_conditioner.pitch = atan2f(-ax, sqrtf(ay * ay + az * az));
        }
        s_imu_conditioner.attitude_initialized = true;
    }

    if (dt < 0.0f)
    {
        dt = 0.0f;
    }
    if (dt > 0.1f)
    {
        dt = 0.1f;
    }

    const float p = sample->gx - s_imu_bias.bias_gx;
    const float q = sample->gy - s_imu_bias.bias_gy;
    const float r = sample->gz - s_imu_bias.bias_gz;
    const float sin_roll = sinf(s_imu_conditioner.roll);
    const float cos_roll = cosf(s_imu_conditioner.roll);
    float cos_pitch = cosf(s_imu_conditioner.pitch);
    if (fabsf(cos_pitch) < 0.1f)
    {
        cos_pitch = (cos_pitch < 0.0f) ? -0.1f : 0.1f;
    }
    const float tan_pitch = sinf(s_imu_conditioner.pitch) / cos_pitch;

    float roll_pred = s_imu_conditioner.roll
                    + (p + sin_roll * tan_pitch * q
                         + cos_roll * tan_pitch * r) * dt;
    float pitch_pred = s_imu_conditioner.pitch
                     + (cos_roll * q - sin_roll * r) * dt;

    /* Accelerometer tilt is valid mainly when its magnitude is close to 1 g.
     * Fade the correction continuously instead of accepting/rejecting it with
     * a hard transition. Gyro propagation carries attitude during motion. */
    float trust = 0.0f;
    const float tolerance = SYS_FUSION_IMU_ATTITUDE_ACC_TOLERANCE;
    if (acc_norm > 0.1f && tolerance > 0.0f)
    {
        trust = 1.0f - fabsf(acc_norm - SYS_FUSION_IMU_GRAVITY_MPS2) / tolerance;
        if (trust < 0.0f) trust = 0.0f;
        if (trust > 1.0f) trust = 1.0f;
    }

    if (trust > 0.0f)
    {
        const float roll_acc = atan2f(ay, az);
        const float pitch_acc = atan2f(-ax, sqrtf(ay * ay + az * az));
        float tau = SYS_FUSION_IMU_ATTITUDE_TIME_CONSTANT_S;
        if (tau < 0.01f) tau = 0.01f;
        const float gain = trust * dt / (tau + dt);
        roll_pred += gain * normalize_angle(roll_acc - roll_pred);
        pitch_pred += gain * normalize_angle(pitch_acc - pitch_pred);
    }

    s_imu_conditioner.roll = normalize_angle(roll_pred);
    /* A chair-mounted IMU should remain far from pitch singularity. The clamp
     * also prevents a damaged sample from making tan(pitch) unbounded. */
    const float pitch_limit = 1.483529864f; /* 85 degrees */
    if (pitch_pred > pitch_limit) pitch_pred = pitch_limit;
    if (pitch_pred < -pitch_limit) pitch_pred = -pitch_limit;
    s_imu_conditioner.pitch = pitch_pred;

    /* Rotate body acceleration into a level frame without applying yaw. At
     * rest gravity maps to level Z, hence level X/Y are linear acceleration
     * and can be consumed by the existing planar UKF without a second yaw. */
    const float sr = sinf(s_imu_conditioner.roll);
    const float cr = cosf(s_imu_conditioner.roll);
    const float sp = sinf(s_imu_conditioner.pitch);
    const float cp = cosf(s_imu_conditioner.pitch);
    sample->ax = cp * ax + sp * sr * ay + sp * cr * az;
    sample->ay = cr * ay - sr * az;
    sample->az = -sp * ax + cp * sr * ay + cp * cr * az
               - SYS_FUSION_IMU_GRAVITY_MPS2;
#else
    (void)sample;
    (void)dt;
#endif
}

static void update_zupt_state(const bsp_imu_data_t *raw, const bsp_imu_data_t *conditioned)
{
#if SYS_FUSION_IMU_ZUPT_ENABLE
    const bsp_imu_data_t *sample = raw;
#if SYS_FUSION_IMU_ZUPT_USE_FILTERED_SAMPLE
    sample = conditioned;
#endif

    if (sample == NULL)
    {
        s_imu_conditioner.zupt_count = 0U;
        s_imu_conditioner.zupt_active = false;
        return;
    }

    float acc_mag;
#if SYS_FUSION_IMU_PREFILTER_ENABLE && SYS_FUSION_IMU_ZUPT_USE_FILTERED_SAMPLE
    acc_mag = sqrtf(sample->ax * sample->ax
                  + sample->ay * sample->ay
                  + sample->az * sample->az);
#elif SYS_FUSION_IMU_PREFILTER_ENABLE
    const float raw_acc_norm = sqrtf(sample->ax * sample->ax
                                   + sample->ay * sample->ay
                                   + sample->az * sample->az);
    acc_mag = fabsf(raw_acc_norm - SYS_FUSION_IMU_GRAVITY_MPS2);
#else
    const float ax = sample->ax - ukf.state.b_ax;
    const float ay = sample->ay - ukf.state.b_ay;
    acc_mag = sqrtf(ax * ax + ay * ay);
#endif
    const float gx = sample->gx - s_imu_bias.bias_gx;
    const float gy = sample->gy - s_imu_bias.bias_gy;
    const float gz = sample->gz - s_imu_bias.bias_gz;
    const float gyr_mag = sqrtf(gx * gx + gy * gy + gz * gz);

    if (acc_mag < SYS_FUSION_IMU_ZUPT_ACC_THRESHOLD &&
        gyr_mag < SYS_FUSION_IMU_ZUPT_GYR_THRESHOLD)
    {
        if (s_imu_conditioner.zupt_count < UINT16_MAX)
        {
            s_imu_conditioner.zupt_count++;
        }
    }
    else
    {
        s_imu_conditioner.zupt_count = 0U;
    }

    s_imu_conditioner.zupt_active =
        (s_imu_conditioner.zupt_count > SYS_FUSION_IMU_ZUPT_COUNT_THRESHOLD);
#else
    (void)raw;
    (void)conditioned;
    s_imu_conditioner.zupt_count = 0U;
    s_imu_conditioner.zupt_active = false;
#endif
}

static bsp_imu_data_t condition_imu_sample(const bsp_imu_data_t *raw, float dt)
{
    bsp_imu_data_t out = {0};
    if (raw == NULL)
    {
        return out;
    }

    out = *raw;

#if SYS_FUSION_IMU_BUTTERWORTH_ENABLE
    if (!s_imu_conditioner.butterworth_initialized)
    {
        reset_biquad_filter(&s_imu_conditioner.ax, raw->ax);
        reset_biquad_filter(&s_imu_conditioner.ay, raw->ay);
        reset_biquad_filter(&s_imu_conditioner.az, raw->az);
        reset_biquad_filter(&s_imu_conditioner.gx, raw->gx);
        reset_biquad_filter(&s_imu_conditioner.gy, raw->gy);
        reset_biquad_filter(&s_imu_conditioner.gz, raw->gz);
        s_imu_conditioner.butterworth_initialized = true;
    }
    else
    {
        out.ax = apply_butterworth_2nd_order(&s_imu_conditioner.ax, raw->ax, dt);
        out.ay = apply_butterworth_2nd_order(&s_imu_conditioner.ay, raw->ay, dt);
        out.az = apply_butterworth_2nd_order(&s_imu_conditioner.az, raw->az, dt);
        out.gx = apply_butterworth_2nd_order(&s_imu_conditioner.gx, raw->gx, dt);
        out.gy = apply_butterworth_2nd_order(&s_imu_conditioner.gy, raw->gy, dt);
        out.gz = apply_butterworth_2nd_order(&s_imu_conditioner.gz, raw->gz, dt);
    }
#endif

    compensate_gravity(&out, dt);

    update_zupt_state(raw, &out);

#if SYS_FUSION_IMU_ZUPT_ENABLE
    if (s_imu_conditioner.zupt_active)
    {
        out.ax = ukf.state.b_ax;
        out.ay = ukf.state.b_ay;
    }
#endif

    return out;
}

static void apply_zupt_velocity_constraint(void)
{
#if SYS_FUSION_IMU_ZUPT_ENABLE
    if (!s_imu_conditioner.zupt_active)
    {
        return;
    }

    ukf.state.vx = 0.0f;
    ukf.state.vy = 0.0f;
    ukf.imu_old.ax = ukf.state.b_ax;
    ukf.imu_old.ay = ukf.state.b_ay;
    ukf.imu_current.ax = ukf.state.b_ax;
    ukf.imu_current.ay = ukf.state.b_ay;

    for (int m = 0; m < NUM_PREDICT_SIGMA; m++)
    {
        ukf.X_sigma_pred[2][m] = 0.0f;
        ukf.X_sigma_pred[3][m] = 0.0f;
    }
#endif
}

static void reset_runtime_state(void)
{
    mw_filter_ukf_init_reset(&s_ukf_init_filter);
    mw_filter_ukf_init_distance_reset(&s_ukf_init_dist_filter);
    reset_imu_conditioner();
    memset(&s_update_diagnostic, 0, sizeof(s_update_diagnostic));

    clear_latest_anchor_metrics();

    s_error_count = 0U;
    s_latest_ranging_error_count = 0U;
    s_prefilter_reject_count = 0U;
    s_last_selected_anchors_mask = 0U;
    s_latest_tril_x = 0.0f;
    s_latest_tril_y = 0.0f;
    s_fusion_dt = 0.0f;
}

static bool active_anchor_index_for_id(uint8_t anchor_id, uint8_t *index_out)
{
    const sys_config_t *cfg = sys_config_get();
    if (!cfg || !index_out || anchor_id == 0U) {
        return false;
    }

    uint32_t count = cfg->anchor_count;
    if (count > NUM_ANCHORS) {
        count = NUM_ANCHORS;
    }

    for (uint32_t i = 0U; i < count; i++) {
        if (cfg->anchor_layout[i].anchor_id == anchor_id) {
            *index_out = (uint8_t)i;
            return true;
        }
    }
    return false;
}

static void clear_latest_anchor_metrics(void)
{
    for (uint8_t i = 0U; i < NUM_ANCHORS; i++) {
        s_latest_distances[i] = 0.0f;
        s_latest_fp_amp_norm[i] = 0.0;
        s_latest_fp_snr[i] = 0.0;
    }

    memset(s_latest_anchor_data, 0, sizeof(s_latest_anchor_data));
    s_latest_anchor_data_count = 0U;
}

void sys_sensor_fusion_prefilter_record_reject(void)
{
    if (s_prefilter_reject_count < UINT32_MAX) {
        s_prefilter_reject_count++;
    }
}

void sys_sensor_fusion_set_ranging_error_count(uint32_t error_count)
{
    s_latest_ranging_error_count = error_count;
}

void sys_sensor_fusion_capture_ranging_snapshot(const uwb_distance_msg_t *ranging_msg)
{
    clear_latest_anchor_metrics();
    s_last_selected_anchors_mask = 0U;

    if (ranging_msg != NULL)
    {
        s_last_selected_anchors_mask = ranging_msg->mask;

        uint32_t count = ranging_msg->count;
        if (count > MAX_ANCHORS_SUPPORTED) {
            count = MAX_ANCHORS_SUPPORTED;
        }

        for (uint32_t i = 0U; i < count; i++)
        {
            const uint8_t aid = ranging_msg->anchor_ids[i];
            uint8_t layout_idx = 0U;
            if (aid == 0U || aid > MAX_ANCHORS_SUPPORTED ||
                (ranging_msg->mask & (1U << (aid - 1U))) == 0U ||
                !active_anchor_index_for_id(aid, &layout_idx)) {
                continue;
            }

            s_latest_distances[layout_idx] = ranging_msg->distances[i];
            s_latest_fp_amp_norm[layout_idx] = ranging_msg->fp_amp_norm[i];
            s_latest_fp_snr[layout_idx] = ranging_msg->fp_snr[i];
        }
    }

    update_latest_anchor_data_snapshot(ranging_msg, NULL);
}

static const mw_tril_anchor_t *find_anchor_by_id(const mw_tril_anchor_t *anchors,
                                                uint8_t anchor_count,
                                                uint8_t anchor_id)
{
    if (!anchors || anchor_id == 0U) {
        return NULL;
    }

    for (uint8_t i = 0U; i < anchor_count; i++) {
        if (anchors[i].valid && anchors[i].id == anchor_id) {
            return &anchors[i];
        }
    }
    return NULL;
}

static void snapshot_latest_anchor_metrics(const mw_tril_anchor_t *candidate_anchors,
                                           uint8_t candidate_count)
{
    const sys_config_t *cfg = sys_config_get();
    if (!cfg || !candidate_anchors) {
        return;
    }

    uint32_t count = cfg->anchor_count;
    if (count > NUM_ANCHORS) {
        count = NUM_ANCHORS;
    }

    for (uint32_t i = 0U; i < count; i++) {
        uint8_t aid = (uint8_t)cfg->anchor_layout[i].anchor_id;
        const mw_tril_anchor_t *candidate =
            find_anchor_by_id(candidate_anchors, candidate_count, aid);
        if (candidate) {
            s_latest_fp_amp_norm[i] = candidate->fp_amp_norm;
            s_latest_fp_snr[i] = candidate->fp_snr;
        }
    }
}

static void update_latest_anchor_data_snapshot(const uwb_distance_msg_t *ranging_msg,
                                               const mw_tril_anchor_t selected_anchors[3])
{
    memset(s_latest_anchor_data, 0, sizeof(s_latest_anchor_data));
    s_latest_anchor_data_count = 0U;

    if (!ranging_msg) {
        return;
    }

    uint32_t count = ranging_msg->count;
    if (count > pb_arraysize(protobuf_sensor_fusion_result_t, anchors)) {
        count = pb_arraysize(protobuf_sensor_fusion_result_t, anchors);
    }
    if (count > MAX_ANCHORS_SUPPORTED) {
        count = MAX_ANCHORS_SUPPORTED;
    }

    for (uint32_t i = 0U; i < count; i++) {
        uint32_t aid = ranging_msg->anchor_ids[i];
        if (aid == 0U || aid > MAX_ANCHORS_SUPPORTED ||
            (ranging_msg->mask & (1U << (aid - 1U))) == 0U) {
            continue;
        }

        protobuf_anchor_data_t *anchor = &s_latest_anchor_data[s_latest_anchor_data_count++];
        anchor->anchor_id   = aid;
        anchor->distance_mm = (ranging_msg->distances[i] > 0.0f)
                            ? (uint32_t)(ranging_msg->distances[i] * 1000.0f)
                            : 0U;
        const mw_tril_anchor_t *selected =
            find_anchor_by_id(selected_anchors, 3U, (uint8_t)aid);
        if (selected != NULL &&
            (s_last_selected_anchors_mask & (1U << (aid - 1U))) != 0U) {
            double fixed2_weight = selected->measurement_weight * 100.0;
            if (!isfinite(fixed2_weight) || fixed2_weight <= 0.0) {
                anchor->weight = 0;
            } else if (fixed2_weight >= (double)INT32_MAX) {
                anchor->weight = INT32_MAX;
            } else {
                anchor->weight = (int32_t)(fixed2_weight + 0.5);
            }
        } else {
            anchor->weight = 0;
        }

    }
}

static int16_t to_uart_fixed2(float value)
{
    float scaled = value * 100.0f;
    if (scaled > 32767.0f) 
    {
        scaled = 32767.0f;
    } 
    else if (scaled < -32768.0f) 
    {
        scaled = -32768.0f;
    }
    return (int16_t)scaled;
}

static int32_t to_proto_fixed2(float value)
{
    return (int32_t)(value * 100.0f);
}

static int32_t to_proto_fixed3(float value)
{
    return to_scaled_i32(value, 1000.0f);
}

static int32_t to_scaled_i32(float value, float scale)
{
    if (!isfinite(value) || !isfinite(scale)) {
        return 0;
    }

    double scaled = (double)value * (double)scale;
    if (scaled >= (double)INT32_MAX) {
        return INT32_MAX;
    }
    if (scaled <= (double)INT32_MIN) {
        return INT32_MIN;
    }
    return (int32_t)lround(scaled);
}

static uint32_t to_mm_u32(float value)
{
    if (!isfinite(value) || value <= 0.0f) {
        return 0U;
    }

    double scaled = (double)value * 1000.0;
    if (scaled >= (double)UINT32_MAX) {
        return UINT32_MAX;
    }
    return (uint32_t)lround(scaled);
}

#if TEST_UKF_STREAM_BLE && ENABLE_SYS_FUSION
static void configure_adv(network_core_t *stream)
{
#ifdef HAVE_BLE_PERIPHERAL
    (void)stream;
    sys_ble_peripheral_set_config();
#else
    (void)stream;
#endif
}
#endif

static float normalize_angle(float angle)
{
    angle = fmodf(angle, SYS_SENSOR_FUSION_2PI);
    if (angle >  SYS_SENSOR_FUSION_PI) angle -= SYS_SENSOR_FUSION_2PI;
    if (angle < -SYS_SENSOR_FUSION_PI) angle += SYS_SENSOR_FUSION_2PI;
    return angle;
}

/* End of file -------------------------------------------------------- */
