phuongmt08/uwb-rtls/firmware/uwb/sys/sys_sensor_fusion.h

/**
 * @file       sys_sensor_fusion.h
 * @copyright  [Your Copyright]
 * @license    [Your License]
 * @version    1.0.0
 * @date       25/03/26
 * @author     Dong Son
 *
 * @brief
 */
/* Define to prevent recursive inclusion ------------------------------ */
#ifndef SYS_SENSOR_FUSION_H_
#define SYS_SENSOR_FUSION_H_

/* Includes ----------------------------------------------------------- */
#include <stdint.h>
#include <stdbool.h>
#include "arm_math.h"
#include <math.h>
#include "mw_trilateration.h"
#include "network/network_core.h"

typedef struct uwb_distance_msg uwb_distance_msg_t;

/* Public defines ----------------------------------------------------- */
#define SYS_SENSOR_FUSION_PI 3.14159265358979323846f

#ifndef TEST_UKF_STREAM_BLE
#define TEST_UKF_STREAM_BLE false
#endif

#ifndef TEST_UKF_STREAM_UART
#define TEST_UKF_STREAM_UART false
#endif

#ifndef TEST_UKF_STREAM_FUSION_LOG
#define TEST_UKF_STREAM_FUSION_LOG false
#endif

#ifndef TEST_UKF_DISTANCE_ZERO_SIMULATION
#define TEST_UKF_DISTANCE_ZERO_SIMULATION 0
#endif

#define UKF_STEP_PREDICT 0U
#define UKF_STEP_UPDATE  1U

/* Public enumerate/structure ----------------------------------------- */
typedef enum
{
	SYS_SENSOR_FUSION_OK = 0,
	SYS_SENSOR_FUSION_ERR,
} sys_sensor_fusion_err_t;

typedef struct
{
    float px;       // Vị trí X (m)
    float py;       // Vị trí Y (m)
    float vx;       // Vận tốc X (m/s)
    float vy;       // Vận tốc Y (m/s)
    float theta;    // Góc Yaw (rad)
    float b_ax;     // Bias Gia tốc X
    float b_ay;     // Bias Gia tốc Y
    float b_gz;     // Bias Gyro Z
} sys_sensor_fusion_data_t;

/* Public macros ------------------------------------------------------ */
/* Public variables --------------------------------------------------- */
/* Public function prototypes ----------------------------------------- */
sys_sensor_fusion_err_t sys_sensor_fusion_init(sys_sensor_fusion_data_t *p_ukf);

sys_sensor_fusion_err_t sys_sensor_fusion_set_initial_position(sys_sensor_fusion_data_t *p_ukf, float x0, float y0);
sys_sensor_fusion_err_t sys_sensor_fusion_realign_position(sys_sensor_fusion_data_t *p_ukf, float x0, float y0);

sys_sensor_fusion_err_t sys_sensor_fusion_predict(sys_sensor_fusion_data_t *p_ukf);

bool sys_sensor_fusion_is_initialized(void);

bool sys_sensor_fusion_get_position_covariance(float *pxx, float *pxy, float *pyy);

void sys_sensor_fusion_prefilter_record_reject(void);
void sys_sensor_fusion_set_ranging_error_count(uint32_t error_count);
void sys_sensor_fusion_capture_ranging_snapshot(const uwb_distance_msg_t *ranging_msg);

bool sys_sensor_fusion_update(sys_sensor_fusion_data_t *p_ukf,
                                                  const vec2d_t *tril_position,
                                                  const mw_tril_anchor_t selected_anchors[3],
                                                  const mw_tril_anchor_t *candidate_anchors,
                                                  uint8_t candidate_count,
                                                  uint8_t selected_anchor_mask,
                                                  const uwb_distance_msg_t *ranging_msg);

void sys_sensor_fusion_report_error(void);

void sys_sensor_fusion_clear_latest_anchor_metrics(void);

void sys_sensor_fusion_reset_error(void);

uint32_t sys_sensor_fusion_get_error_count(void);

void sys_sensor_fusion_reset(void);

void sys_sensor_fusion_stream_ble(uint8_t ukf_step);

void sys_sensor_fusion_stream_uart(uint8_t ukf_step);

void sys_sensor_fusion_task();

float sys_sensor_fusion_get_ukf_yaw_deg();

float sys_sensor_fusion_get_yaw_deg();

sys_sensor_fusion_err_t sys_sensor_fusion_set_update_flag();

sys_sensor_fusion_err_t sys_sensor_fusion_clear_update_flag();

sys_sensor_fusion_err_t sys_sensor_fusion_set_predict_flag();

sys_sensor_fusion_err_t sys_sensor_fusion_clear_predict_flag();

bool sys_sensor_fusion_check_update_flag();

bool sys_sensor_fusion_check_predict_flag();

void sys_sensor_fusion_set_initial_yaw(uint32_t yaw_deg);

#endif /* SYS_SENSOR_FUSION_H_ */

/* End of file -------------------------------------------------------- */
