phuongmt08/uwb-rtls/firmware/ble_firmware/peripheral/config/board.h

/**
 * Custom board definition for FSC-BT630 (nRF52832)
 * Based on schematic: BLE module with UART interface + status LED
 */

#ifndef FSC_BT630_H
#define FSC_BT630_H

#ifdef __cplusplus
extern "C" {
#endif

#include "nrf_gpio.h"

// ─── LEDs ────────────────────────────────────────────────────────────────────
// D8 GREEN LED via R19 (2.2k) connected to P0.02/AIN0 (module pin 11)
#define LEDS_NUMBER     1

#define LED1_G          NRF_GPIO_PIN_MAP(0, 2)   // P0.02 - Green LED D8

#define LED_1           LED1_G

#define LEDS_ACTIVE_STATE 0                       // Active LOW (common cathode to GND)

#define LEDS_LIST       { LED_1 }
#define LEDS_INV_MASK   LEDS_MASK

#define BSP_LED_0       LED_1

// ─── Buttons ─────────────────────────────────────────────────────────────────
// No user button in schematic
#define BUTTONS_NUMBER  0
#define BUTTONS_LIST    { }

// ─── UART (nối với gateway nRF52840 qua BLE_TX/BLE_RX) ───────────────────────
// FSC-BT630 default UART pins (nRF52832 internal mapping)
#define RX_PIN_NUMBER   NRF_GPIO_PIN_MAP(0, 8)   // P0.08 → UART_RX (BLE_RX from gateway)
#define TX_PIN_NUMBER   NRF_GPIO_PIN_MAP(0, 6)   // P0.06 → UART_TX (BLE_TX to gateway)
#define CTS_PIN_NUMBER  NRF_GPIO_PIN_MAP(0, 7)   // P0.07 → CTS
#define RTS_PIN_NUMBER  NRF_GPIO_PIN_MAP(0, 5)   // P0.05 → RTS
#define HWFC            true

// ─── SWD (debug interface) ────────────────────────────────────────────────────
// BLE_SWDIO → pin 8 (SWDIO), BLE_SWDCLK → pin 7 (SWDCLK)
// BLE_RST   → pin 6 (RESET)

// ─── GPIO khả dụng trên module ────────────────────────────────────────────────
// Pin 11: P0.02/AIN0  → LED D8
// Pin 12: P0.03/AIN1  → free
// Pin 13: P0.04/AIN2  → free
// Pin 14: P0.05/AIN3  → RTS
// Pin 15: P0.06       → UART_TX
// Pin 16: P0.07       → CTS
// Pin 17: P0.08       → UART_RX
// Pin 18: P0.09/NFC1  → free (avoid if using NFC)
// Pin 19: P0.10/NFC2  → free (avoid if using NFC)
// Pin 20: P0.11       → free

#ifdef __cplusplus
}
#endif

#endif // FSC_BT630_H
