phuongmt08/uwb-rtls/firmware/ble_firmware/ble_common/ble_bridge/bb_broadcast.c

/**
 * @file       bb_broadcast.c
 * @copyright  [Your Copyright]
 * @license    [Your License]
 * @version    1.0.0
 * @date       2026-07-21
 * @author     Phuong Mai
 *
 * @brief      Self-contained BLE broadcast module (TX + RX). See bb_broadcast.h.
 *
 *             Broadcast uses its own advertising set on roles without an
 *             advertiser (central). A role that already owns the SoftDevice's
 *             single advertising set (peripheral) lends that handle for one
 *             short burst through the optional arbitration hooks. On the
 *             peripheral this module also owns a duty-cycled scanner for RX;
 *             on the central it piggybacks on the application scanner.
 */
/* Includes ----------------------------------------------------------- */
#include "bb_broadcast.h"

#include <string.h>

#include "ble.h"
#include "ble_advdata.h"
#include "nrf_sdh_ble.h"
#include "app_timer.h"
#include "app_util.h"
#include "nrf_log.h"

#include "ble_config.h"

/* Private defines ---------------------------------------------------- */
#define BB_BROADCAST_MAGIC              0xB7u
#define BB_BROADCAST_VERSION            0x01u
#define BB_BROADCAST_AD_TYPE_MANUF      0xFFu
#define BB_BROADCAST_AD_TYPE_FLAGS      0x01u
#define BB_BROADCAST_FLAGS_GENERAL      0x06u
#define BB_BROADCAST_HEADER_SIZE        8u

#define BB_BROADCAST_CONN_CFG_TAG       1
/* Must run before nrf_ble_scan (priority 1). That module re-arms scanning and
 * returns the ADV buffer to SoftDevice before later observers can parse it. */
#define BB_BROADCAST_OBSERVER_PRIO      0

/* Legacy fragmentation: ADV events aired per fragment. */
#define BB_BROADCAST_ADV_EVENTS_PER_FRAGMENT   3u

/* TX burst watchdog: recover if a burst never terminates. */
#define BB_BROADCAST_WATCHDOG_MS        3000u

/* RX reassembly (legacy path). */
#define BB_BROADCAST_REASSEMBLY_TIMEOUT_MS     1000u
#if defined(BLE_CENTRAL)
#define BB_BROADCAST_RX_CONTEXTS        4u
#else
#define BB_BROADCAST_RX_CONTEXTS        2u
#endif

/* Continuous RX lets a short burst complete quickly and keeps the 3-second
 * retry policy at the router level instead of using a scan duty-cycle delay. */
#ifndef BB_BROADCAST_SCAN_INTERVAL_MS
#define BB_BROADCAST_SCAN_INTERVAL_MS   30u
#endif
#ifndef BB_BROADCAST_SCAN_WINDOW_MS
#define BB_BROADCAST_SCAN_WINDOW_MS     30u
#endif

/* Private enumerate/structure ---------------------------------------- */
typedef struct
{
    bool active;
    uint8_t addr[BLE_GAP_ADDR_LEN];
    uint8_t addr_type;
    bb_broadcast_reassembly_t reassembly;
} bb_broadcast_rx_slot_t;

/* Private macros ----------------------------------------------------- */
/* Public variables --------------------------------------------------- */
/* Private variables -------------------------------------------------- */
static bb_broadcast_rx_cb_t m_rx_cb = NULL;
static bool m_initialized = false;

/* ---- TX ---- */
static uint8_t  m_bcast_adv_handle = BLE_GAP_ADV_SET_HANDLE_NOT_SET;
static bb_broadcast_adv_acquire_cb_t m_adv_acquire_cb = NULL;
static bb_broadcast_adv_release_cb_t m_adv_release_cb = NULL;
static bool     m_adv_handle_borrowed = false;
static bool     m_bcast_adv_started = false;
#if BLE_BROADCAST_USE_EXTENDED
static uint8_t  m_bcast_advdata[BLE_GAP_ADV_SET_DATA_SIZE_EXTENDED_MAX_SUPPORTED];
#else
static uint8_t  m_bcast_advdata[BLE_GAP_ADV_SET_DATA_SIZE_MAX];
#endif
static uint8_t  m_bcast_packet[BLE_BROADCAST_MAX_PACKET_SIZE];
static uint8_t  m_bcast_packet_len = 0;
static uint8_t  m_bcast_seq = 0;
static uint8_t  m_bcast_frag_index = 0;
static uint8_t  m_bcast_frag_count = 0;
static bool     m_bcast_active = false;
static uint32_t m_bcast_start_tick = 0;
#if BLE_BROADCAST_USE_EXTENDED
static bool     m_bcast_use_typed_legacy = false;
#endif

static ble_gap_adv_data_t m_bcast_adv_data =
{
    .adv_data      = { .p_data = m_bcast_advdata, .len = 0 },
    .scan_rsp_data = { .p_data = NULL, .len = 0 },
};

/* ---- RX ---- */
static bb_broadcast_rx_slot_t m_rx_slots[BB_BROADCAST_RX_CONTEXTS];
static uint8_t  m_rx_packet[BLE_BROADCAST_MAX_PACKET_SIZE];

#if defined(BLE_PERIPHERAL)
static uint8_t  m_scan_buffer_data[BLE_GAP_SCAN_BUFFER_EXTENDED_MIN];
static ble_data_t m_scan_buffer = { .p_data = m_scan_buffer_data, .len = sizeof(m_scan_buffer_data) };
static bool     m_scan_active = false;
#endif

/* Private function prototypes ---------------------------------------- */
static uint8_t bb_broadcast_fragment_count(uint8_t packet_len);
static ret_code_t bcast_start_current_fragment(void);
static void bcast_advance_fragment(void);
static void bcast_finish(bool stop_advertising);
static bb_broadcast_rx_slot_t *rx_slot_get(ble_gap_addr_t const *addr);
static void rx_scan_report_handle(ble_gap_evt_adv_report_t const *p_adv_report);
static void bb_broadcast_ble_evt(ble_evt_t const *p_ble_evt, void *p_context);
#if defined(BLE_PERIPHERAL)
static void rx_scan_start(void);
#endif

/* Function definitions ----------------------------------------------- */
/* ----- Wire-format helpers ------------------------------------------ */
static uint8_t bb_broadcast_fragment_count(uint8_t packet_len)
{
    return (uint8_t)((packet_len + BLE_BROADCAST_FRAGMENT_PAYLOAD_SIZE - 1u) /
                     BLE_BROADCAST_FRAGMENT_PAYLOAD_SIZE);
}

uint16_t bb_broadcast_crc16(const uint8_t *data, uint8_t len)
{
    uint16_t crc = 0xFFFFu;

    if (data == NULL)
    {
        return crc;
    }

    for (uint8_t i = 0; i < len; i++)
    {
        crc ^= (uint16_t)data[i] << 8;
        for (uint8_t bit = 0; bit < 8u; bit++)
        {
            if ((crc & 0x8000u) != 0u)
            {
                crc = (uint16_t)((crc << 1) ^ 0x1021u);
            }
            else
            {
                crc <<= 1;
            }
        }
    }

    return crc;
}

bool bb_broadcast_encode_fragment(const uint8_t *packet,
                                  uint8_t packet_len,
                                  uint8_t seq,
                                  uint8_t frag_index,
                                  uint8_t *out,
                                  uint8_t out_size,
                                  uint8_t *out_len)
{
    if (packet == NULL || out == NULL || out_len == NULL || packet_len == 0u ||
        packet_len > BLE_BROADCAST_MAX_PACKET_SIZE)
    {
        return false;
    }

    uint8_t frag_count = bb_broadcast_fragment_count(packet_len);
    if (frag_count == 0u || frag_count > BLE_BROADCAST_MAX_FRAGMENTS ||
        frag_index >= frag_count || out_size < BB_BROADCAST_HEADER_SIZE)
    {
        return false;
    }

    uint8_t offset = (uint8_t)(frag_index * BLE_BROADCAST_FRAGMENT_PAYLOAD_SIZE);
    uint8_t remaining = (uint8_t)(packet_len - offset);
    uint8_t payload_len = remaining > BLE_BROADCAST_FRAGMENT_PAYLOAD_SIZE ?
                          BLE_BROADCAST_FRAGMENT_PAYLOAD_SIZE :
                          remaining;

    if (out_size < (uint8_t)(BB_BROADCAST_HEADER_SIZE + payload_len))
    {
        return false;
    }

    uint16_t crc = bb_broadcast_crc16(packet, packet_len);
    out[0] = BB_BROADCAST_MAGIC;
    out[1] = BB_BROADCAST_VERSION;
    out[2] = seq;
    out[3] = frag_index;
    out[4] = frag_count;
    out[5] = packet_len;
    out[6] = (uint8_t)(crc & 0xFFu);
    out[7] = (uint8_t)(crc >> 8);
    memcpy(&out[BB_BROADCAST_HEADER_SIZE], &packet[offset], payload_len);

    *out_len = (uint8_t)(BB_BROADCAST_HEADER_SIZE + payload_len);
    return true;
}

bool bb_broadcast_decode_fragment(const uint8_t *manuf_data,
                                  uint8_t manuf_data_len,
                                  bb_broadcast_fragment_t *fragment)
{
    if (manuf_data == NULL || fragment == NULL ||
        manuf_data_len < BB_BROADCAST_HEADER_SIZE ||
        manuf_data_len > BLE_BROADCAST_MANUF_DATA_MAX_SIZE)
    {
        return false;
    }

    if (manuf_data[0] != BB_BROADCAST_MAGIC ||
        manuf_data[1] != BB_BROADCAST_VERSION)
    {
        return false;
    }

    uint8_t frag_index = manuf_data[3];
    uint8_t frag_count = manuf_data[4];
    uint8_t total_len = manuf_data[5];
    uint8_t payload_len = (uint8_t)(manuf_data_len - BB_BROADCAST_HEADER_SIZE);

    if (total_len == 0u || total_len > BLE_BROADCAST_MAX_PACKET_SIZE ||
        frag_count == 0u || frag_count > BLE_BROADCAST_MAX_FRAGMENTS ||
        frag_count != bb_broadcast_fragment_count(total_len) ||
        frag_index >= frag_count || payload_len == 0u ||
        payload_len > BLE_BROADCAST_FRAGMENT_PAYLOAD_SIZE)
    {
        return false;
    }

    uint8_t expected_payload = BLE_BROADCAST_FRAGMENT_PAYLOAD_SIZE;
    if (frag_index == (uint8_t)(frag_count - 1u))
    {
        uint8_t last_offset = (uint8_t)(frag_index * BLE_BROADCAST_FRAGMENT_PAYLOAD_SIZE);
        expected_payload = (uint8_t)(total_len - last_offset);
    }

    if (payload_len != expected_payload)
    {
        return false;
    }

    fragment->seq = manuf_data[2];
    fragment->frag_index = frag_index;
    fragment->frag_count = frag_count;
    fragment->total_len = total_len;
    fragment->crc16 = (uint16_t)manuf_data[6] | ((uint16_t)manuf_data[7] << 8);
    fragment->payload = &manuf_data[BB_BROADCAST_HEADER_SIZE];
    fragment->payload_len = payload_len;
    return true;
}

bool bb_broadcast_find_fragment(const uint8_t *adv_data,
                                uint16_t adv_data_len,
                                bb_broadcast_fragment_t *fragment)
{
    if (adv_data == NULL || fragment == NULL)
    {
        return false;
    }

    uint16_t pos = 0;
    while (pos < adv_data_len)
    {
        uint8_t field_len = adv_data[pos++];
        if (field_len == 0u)
        {
            break;
        }
        if ((uint16_t)(pos + field_len) > adv_data_len)
        {
            return false;
        }

        uint8_t ad_type = adv_data[pos];
        const uint8_t *field_data = &adv_data[pos + 1u];
        uint8_t field_data_len = (uint8_t)(field_len - 1u);

        if (ad_type == BB_BROADCAST_AD_TYPE_MANUF && field_data_len >= 2u)
        {
            uint16_t company_id = (uint16_t)field_data[0] | ((uint16_t)field_data[1] << 8);
            if (company_id == BLE_BROADCAST_COMPANY_ID)
            {
                return bb_broadcast_decode_fragment(&field_data[2],
                                                    (uint8_t)(field_data_len - 2u),
                                                    fragment);
            }
        }

        pos = (uint16_t)(pos + field_len);
    }

    return false;
}

bool bb_broadcast_build_adv_data(const uint8_t *manuf_data,
                                 uint8_t manuf_data_len,
                                 uint8_t *adv_data,
                                 uint8_t adv_data_size,
                                 uint8_t *adv_data_len)
{
    if (manuf_data == NULL || adv_data == NULL || adv_data_len == NULL ||
        manuf_data_len == 0u ||
        manuf_data_len > BLE_BROADCAST_MANUF_DATA_MAX_SIZE)
    {
        return false;
    }

    uint8_t total_len = (uint8_t)(7u + manuf_data_len);
    if (adv_data_size < total_len || total_len > BLE_BROADCAST_ADV_DATA_MAX_SIZE)
    {
        return false;
    }

    adv_data[0] = 2u;
    adv_data[1] = BB_BROADCAST_AD_TYPE_FLAGS;
    adv_data[2] = BB_BROADCAST_FLAGS_GENERAL;
    adv_data[3] = (uint8_t)(1u + 2u + manuf_data_len);
    adv_data[4] = BB_BROADCAST_AD_TYPE_MANUF;
    adv_data[5] = (uint8_t)(BLE_BROADCAST_COMPANY_ID & 0xFFu);
    adv_data[6] = (uint8_t)(BLE_BROADCAST_COMPANY_ID >> 8);
    memcpy(&adv_data[7], manuf_data, manuf_data_len);

    *adv_data_len = total_len;
    return true;
}

void bb_broadcast_reassembly_reset(bb_broadcast_reassembly_t *ctx)
{
    if (ctx != NULL)
    {
        memset(ctx, 0, sizeof(*ctx));
    }
}

bool bb_broadcast_reassembly_push(bb_broadcast_reassembly_t *ctx,
                                  const bb_broadcast_fragment_t *fragment,
                                  uint32_t now_tick,
                                  uint32_t timeout_ticks,
                                  uint8_t *out_packet,
                                  uint8_t out_size,
                                  uint8_t *out_len)
{
    if (ctx == NULL || fragment == NULL || out_packet == NULL || out_len == NULL ||
        out_size < fragment->total_len)
    {
        return false;
    }

    bool expired = ctx->active &&
                   timeout_ticks != 0u &&
                   (uint32_t)(now_tick - ctx->last_tick) > timeout_ticks;

    if (!ctx->active || expired ||
        ctx->seq != fragment->seq ||
        ctx->frag_count != fragment->frag_count ||
        ctx->total_len != fragment->total_len ||
        ctx->crc16 != fragment->crc16)
    {
        bb_broadcast_reassembly_reset(ctx);
        ctx->active = true;
        ctx->seq = fragment->seq;
        ctx->frag_count = fragment->frag_count;
        ctx->total_len = fragment->total_len;
        ctx->crc16 = fragment->crc16;
    }

    uint8_t offset = (uint8_t)(fragment->frag_index * BLE_BROADCAST_FRAGMENT_PAYLOAD_SIZE);
    if ((uint16_t)offset + fragment->payload_len > ctx->total_len)
    {
        return false;
    }

    memcpy(&ctx->packet[offset], fragment->payload, fragment->payload_len);
    ctx->received_mask |= (uint16_t)(1u << fragment->frag_index);
    ctx->last_tick = now_tick;

    uint16_t complete_mask = (uint16_t)((1u << ctx->frag_count) - 1u);
    if ((ctx->received_mask & complete_mask) != complete_mask)
    {
        return false;
    }

    if (bb_broadcast_crc16(ctx->packet, ctx->total_len) != ctx->crc16)
    {
        bb_broadcast_reassembly_reset(ctx);
        return false;
    }

    memcpy(out_packet, ctx->packet, ctx->total_len);
    *out_len = ctx->total_len;
    bb_broadcast_reassembly_reset(ctx);
    return true;
}

/* ----- TX: burst state machine -------------------------------------- */
static ret_code_t bcast_start_current_fragment(void)
{
    ret_code_t err_code;
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
